ccmteamap/robot/3D_MODELS/3D_PCB.JPG

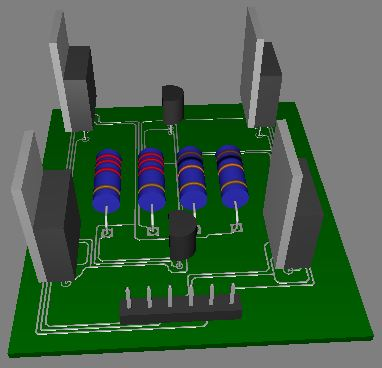
3D_MODELS/3D_PCB.JPG
