ccmteamap/robot/docs/analyse/mindmap.png

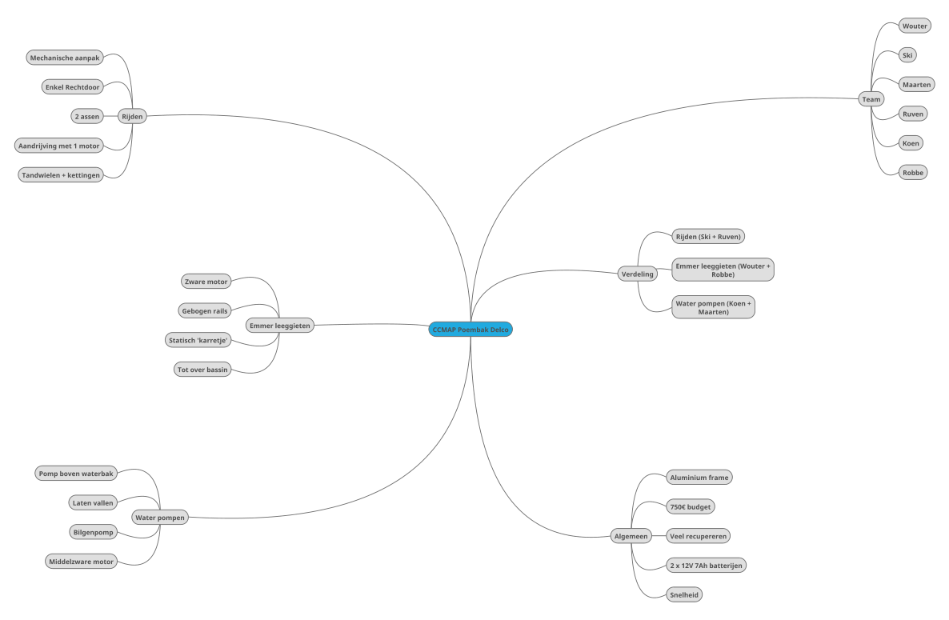
docs/analyse/mindmap.png
