ccmteamap/robot/docs/animations/pdelcogiforiginalfiles/001.jpg

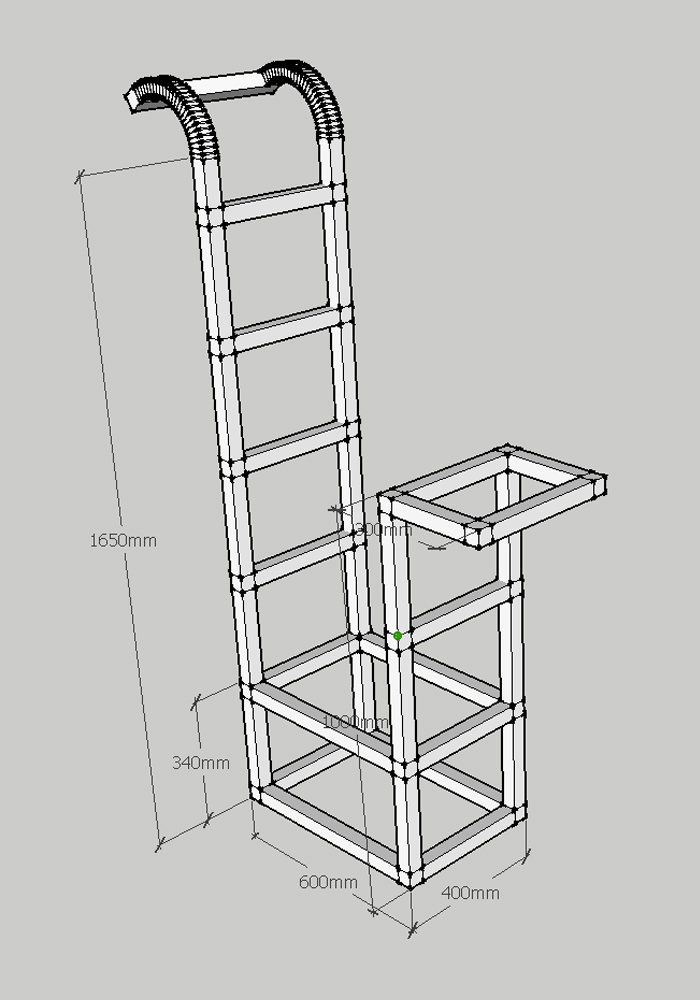
docs/animations/pdelcogiforiginalfiles/001.jpg
