ccmteamap/robot/docs/animations/pdelcogiforiginalfiles/003.jpg

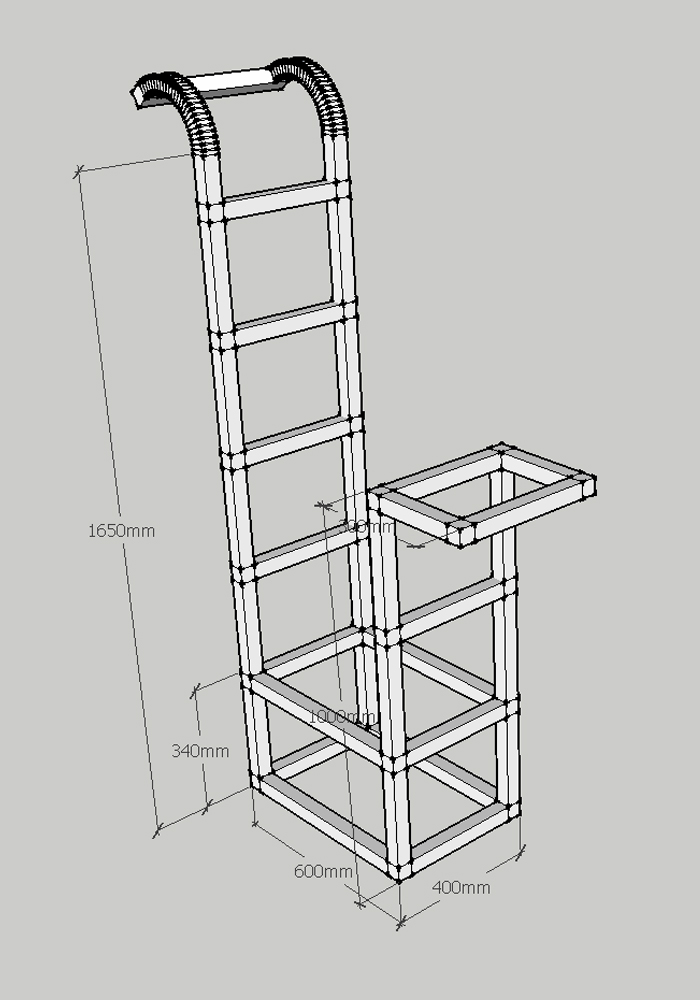
docs/animations/pdelcogiforiginalfiles/003.jpg
