ccmteamap/robot/docs/animations/pdelcogiforiginalfiles/005.jpg

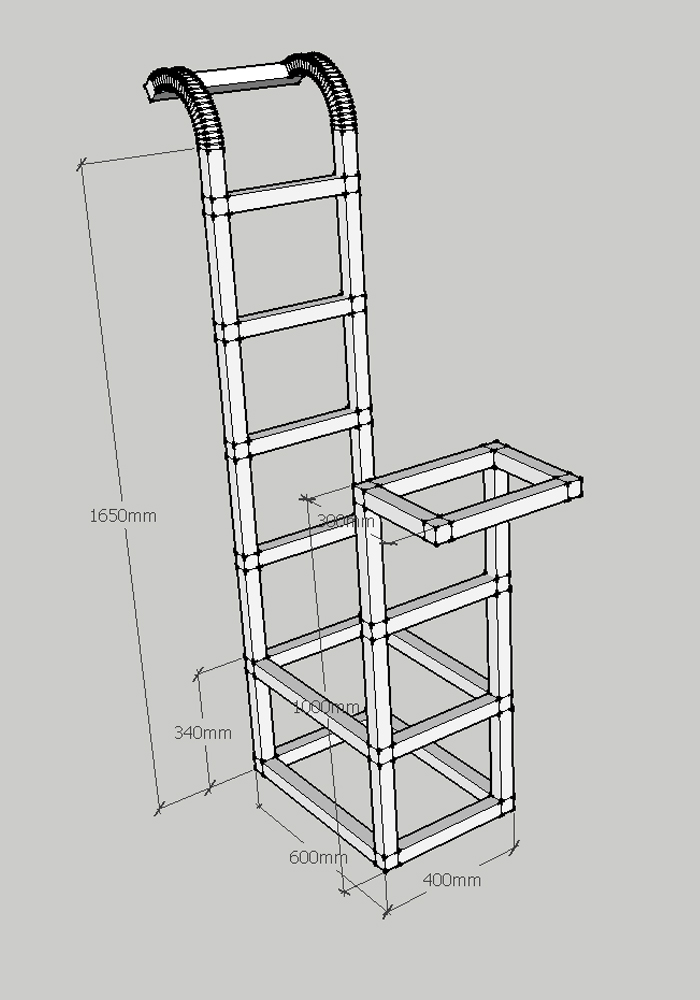
docs/animations/pdelcogiforiginalfiles/005.jpg
