ccmteamap/robot/docs/animations/pdelcogiforiginalfiles/006.jpg

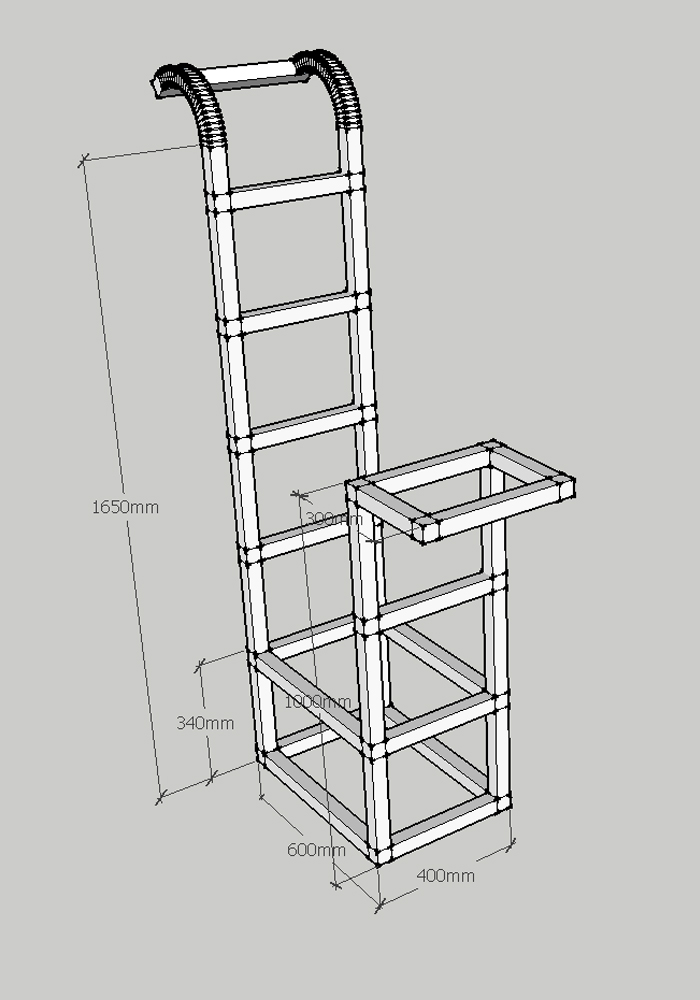
docs/animations/pdelcogiforiginalfiles/006.jpg
