ccmteamap/robot/docs/animations/pdelcogiforiginalfiles/008.jpg

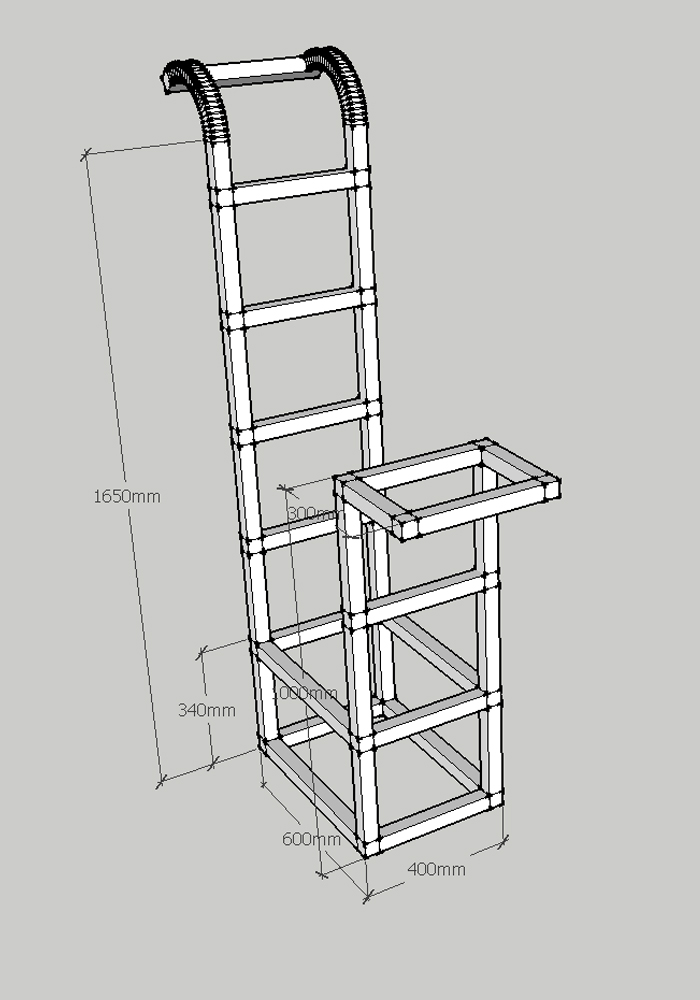
docs/animations/pdelcogiforiginalfiles/008.jpg
