ccmteamap/robot/docs/animations/pdelcogiforiginalfiles/012.jpg

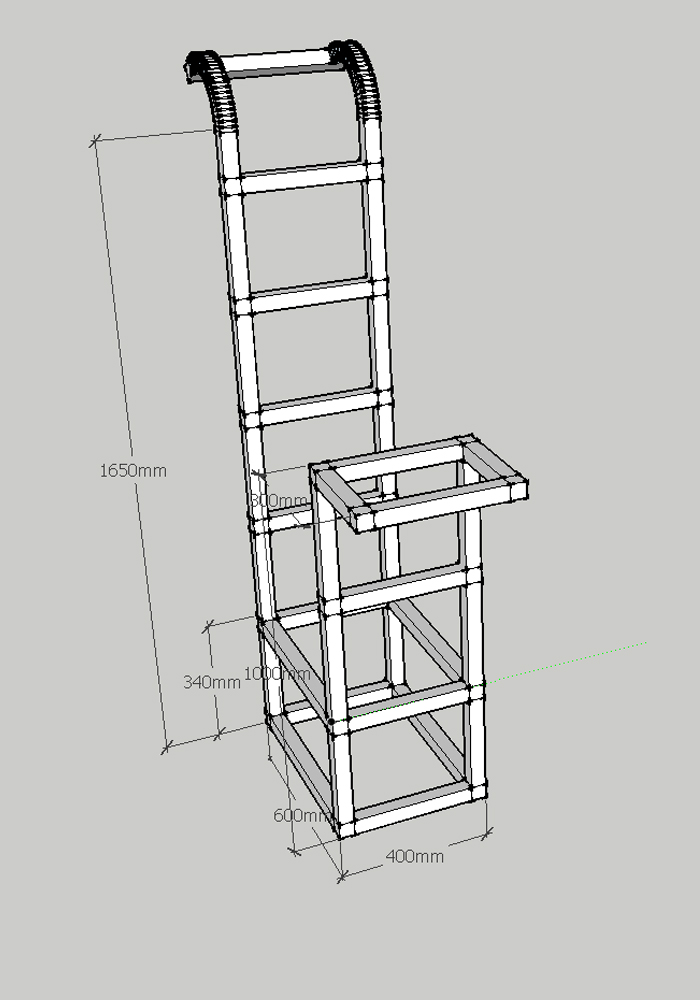
docs/animations/pdelcogiforiginalfiles/012.jpg
