ccmteamap/robot/docs/animations/pdelcogiforiginalfiles/014.jpg

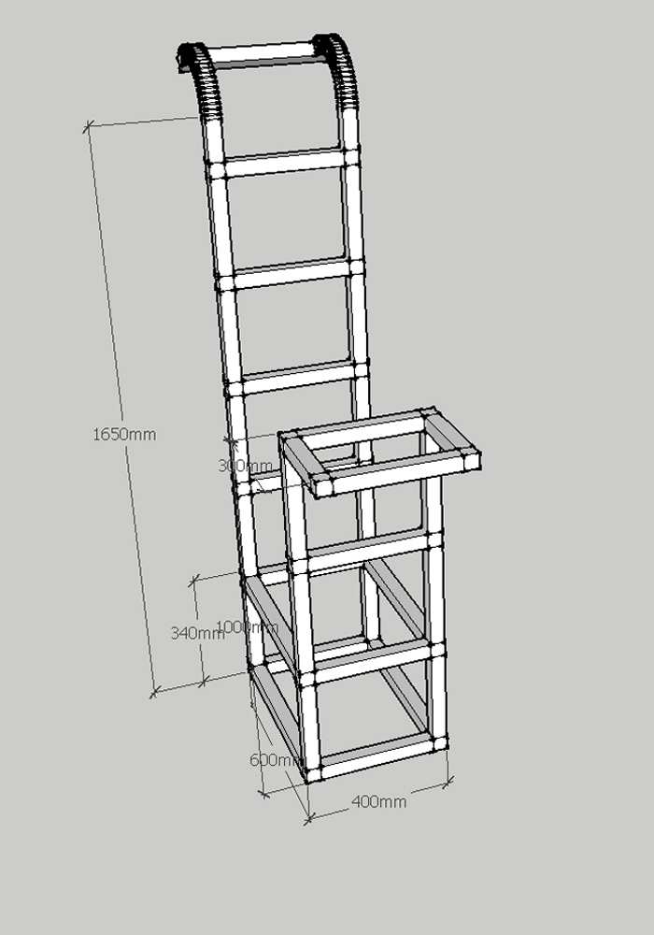
docs/animations/pdelcogiforiginalfiles/014.jpg
