ccmteamap/robot/docs/animations/pdelcogiforiginalfiles/015.jpg

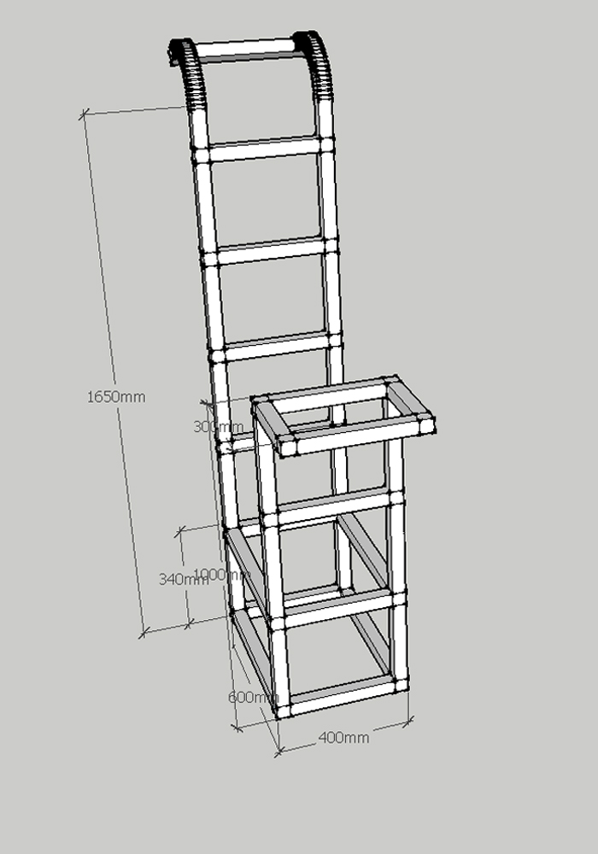
docs/animations/pdelcogiforiginalfiles/015.jpg
