ccmteamap/robot/docs/animations/pdelcogiforiginalfiles/016.jpg

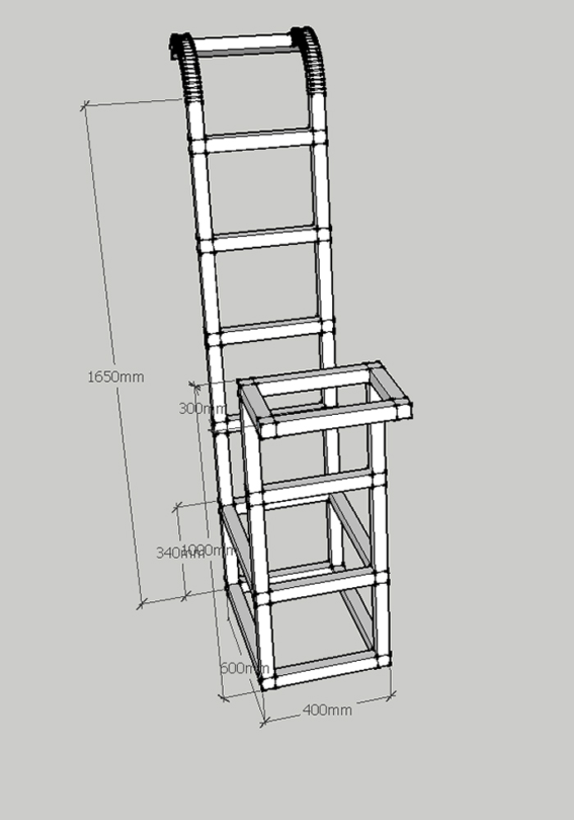
docs/animations/pdelcogiforiginalfiles/016.jpg
