ccmteamap/robot/docs/animations/pdelcogiforiginalfiles/017.jpg

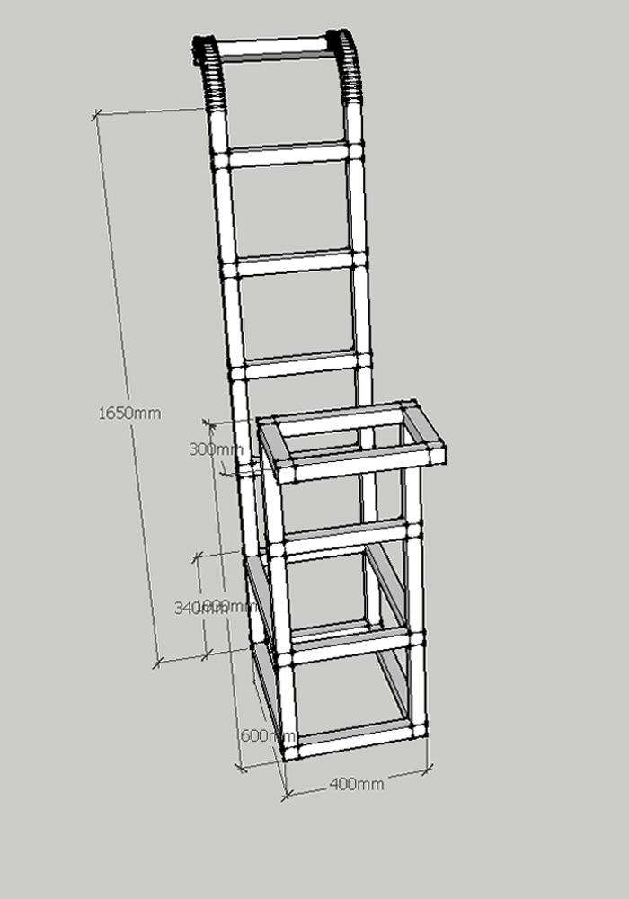
docs/animations/pdelcogiforiginalfiles/017.jpg
