ccmteamap/robot/docs/animations/pdelcogiforiginalfiles/018.jpg

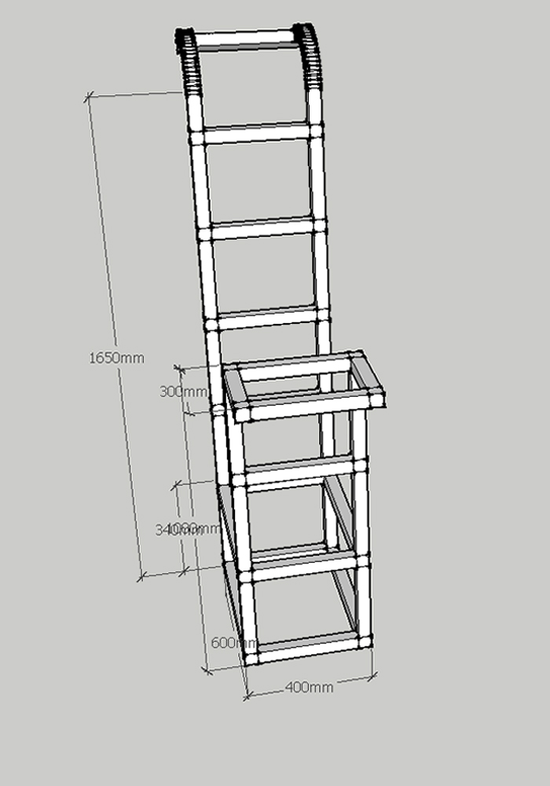
docs/animations/pdelcogiforiginalfiles/018.jpg
