ccmteamap/robot/docs/animations/pdelcogiforiginalfiles/020.jpg

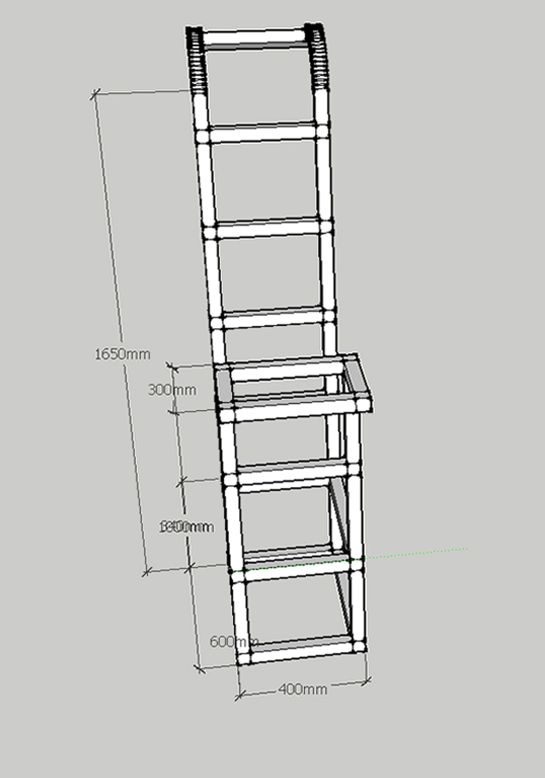
docs/animations/pdelcogiforiginalfiles/020.jpg
