ccmteamap/robot/docs/animations/pdelcogiforiginalfiles/021.jpg

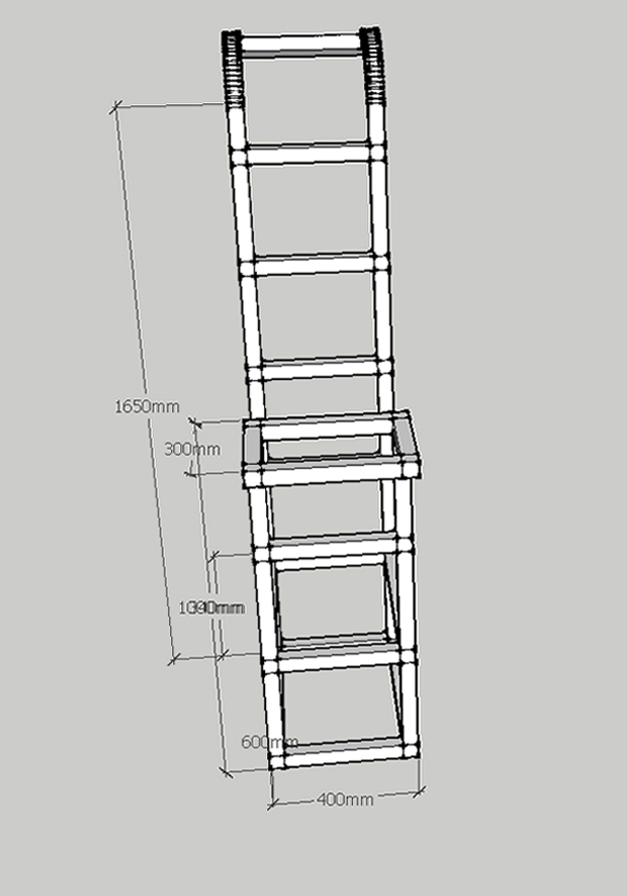
docs/animations/pdelcogiforiginalfiles/021.jpg
