ccmteamap/robot/docs/animations/pdelcogiforiginalfiles/022.jpg

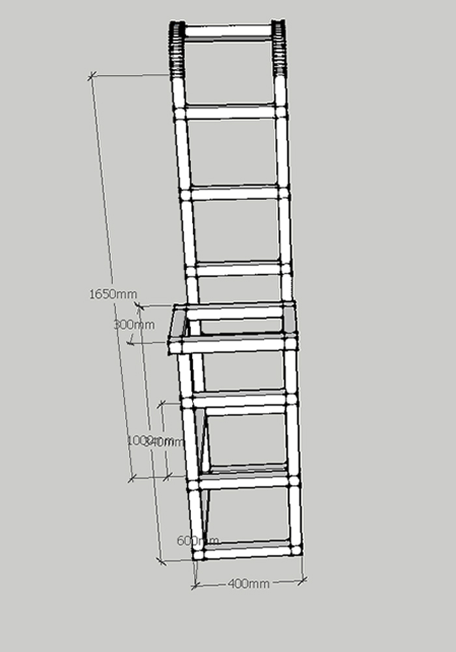
docs/animations/pdelcogiforiginalfiles/022.jpg
