ccmteamap/robot/docs/animations/pdelcogiforiginalfiles/024.jpg

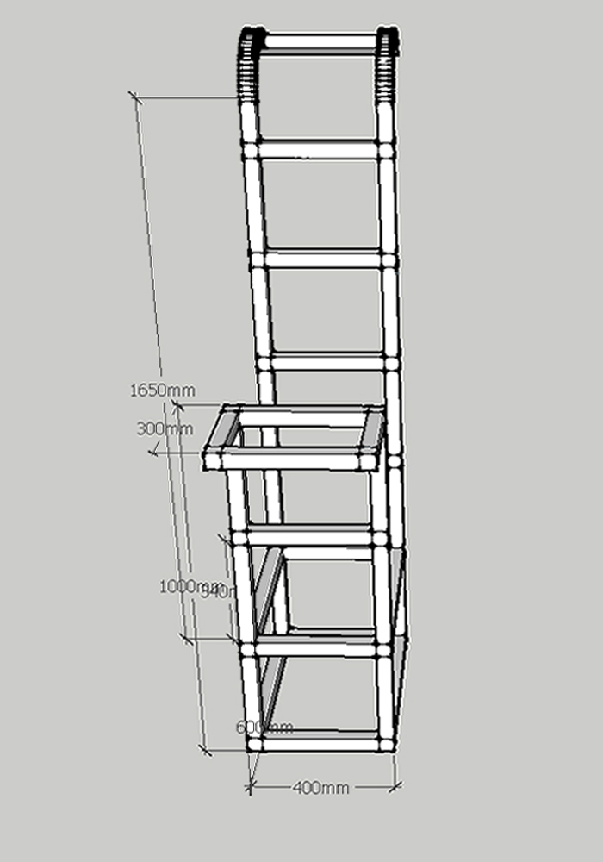
docs/animations/pdelcogiforiginalfiles/024.jpg
