ccmteamap/robot/docs/animations/pdelcogiforiginalfiles/025.jpg

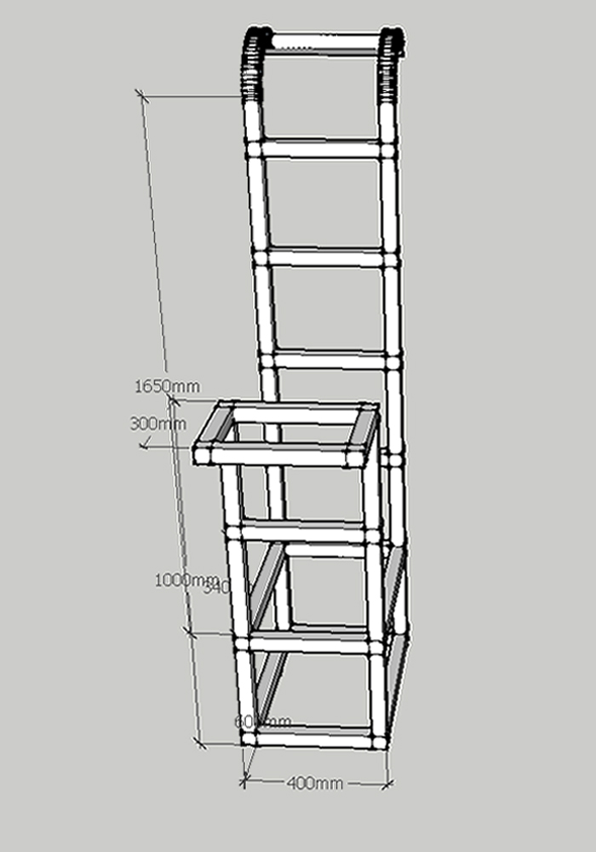
docs/animations/pdelcogiforiginalfiles/025.jpg
