ccmteamap/robot/docs/animations/pdelcogiforiginalfiles/026.jpg

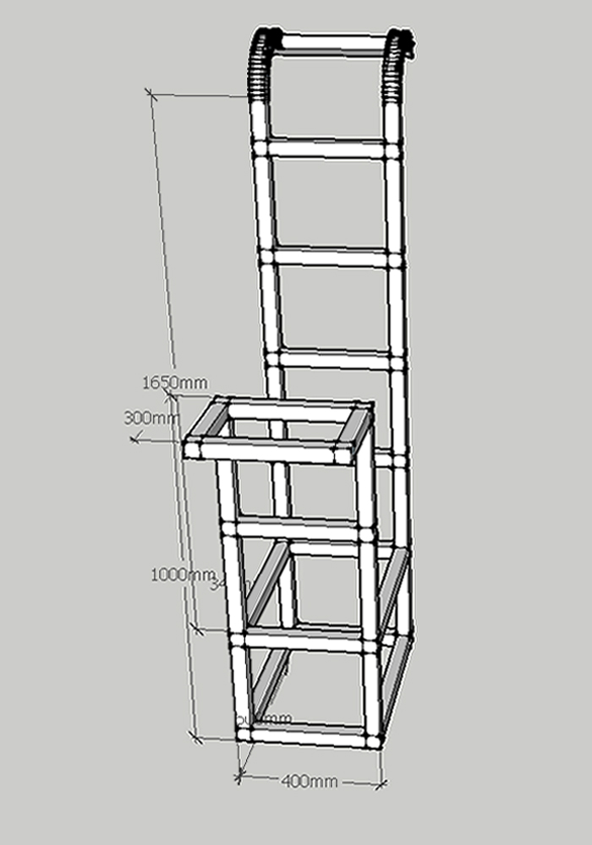
docs/animations/pdelcogiforiginalfiles/026.jpg
