ccmteamap/robot/docs/animations/pdelcogiforiginalfiles/027.jpg

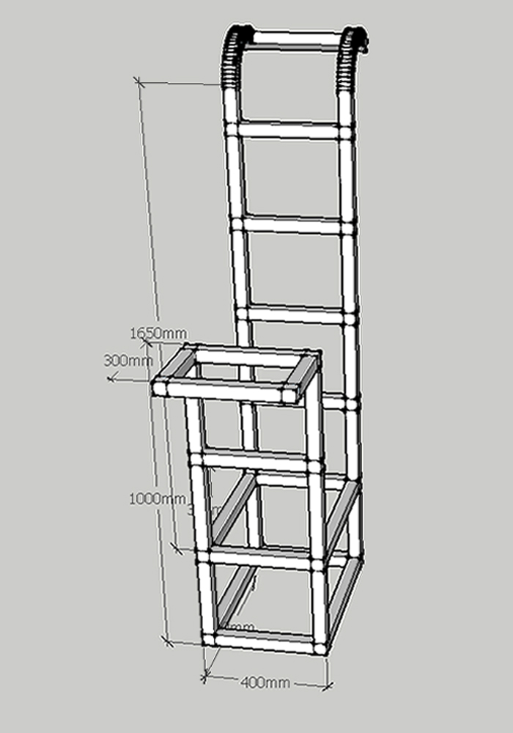
docs/animations/pdelcogiforiginalfiles/027.jpg
