ccmteamap/robot/docs/animations/pdelcogiforiginalfiles/028.jpg

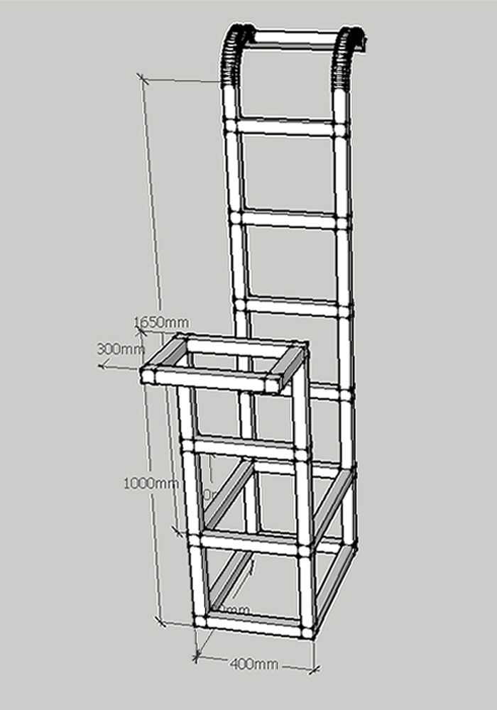
docs/animations/pdelcogiforiginalfiles/028.jpg
