ccmteamap/robot/docs/animations/pdelcogiforiginalfiles/031.jpg

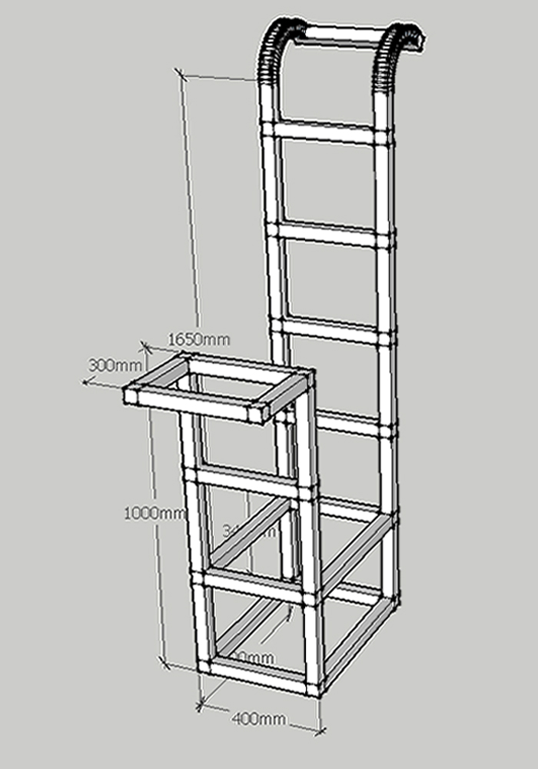
docs/animations/pdelcogiforiginalfiles/031.jpg
