ccmteamap/robot/docs/animations/pdelcogiforiginalfiles/032.jpg

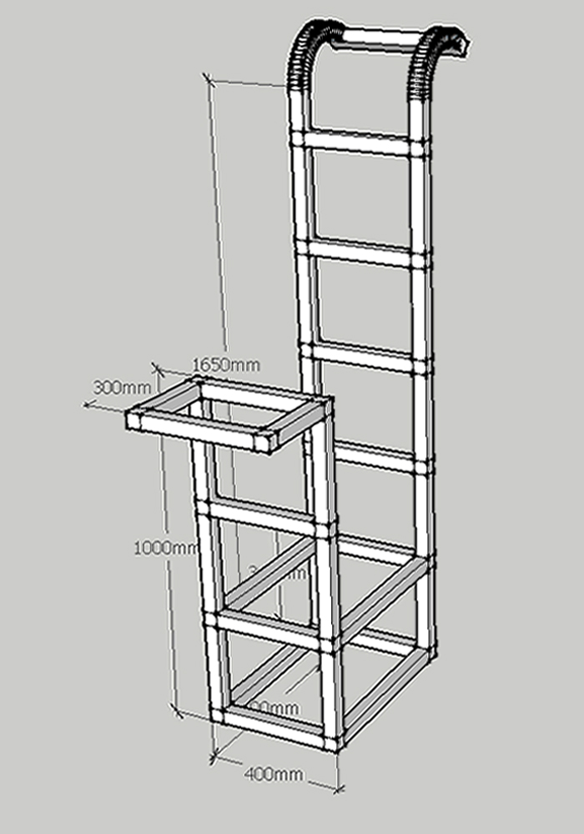
docs/animations/pdelcogiforiginalfiles/032.jpg
