ccmteamap/robot/docs/animations/pdelcogiforiginalfiles/033.jpg

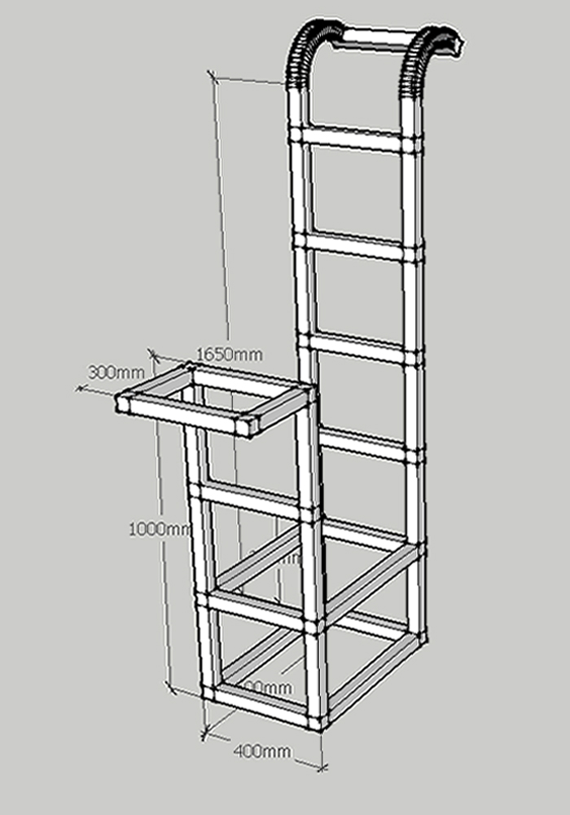
docs/animations/pdelcogiforiginalfiles/033.jpg
