ccmteamap/robot/docs/animations/pdelcogiforiginalfiles/034.jpg

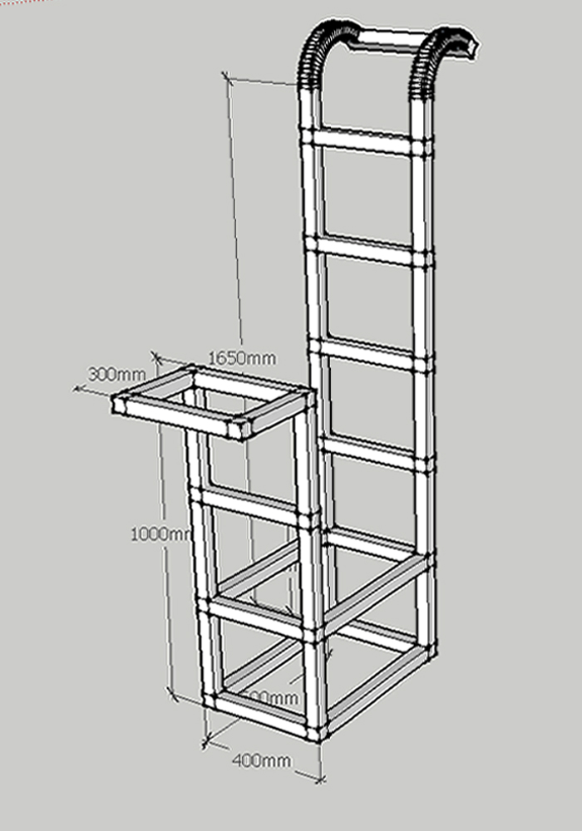
docs/animations/pdelcogiforiginalfiles/034.jpg
