ccmteamap/robot/docs/animations/pdelcogiforiginalfiles/035.jpg

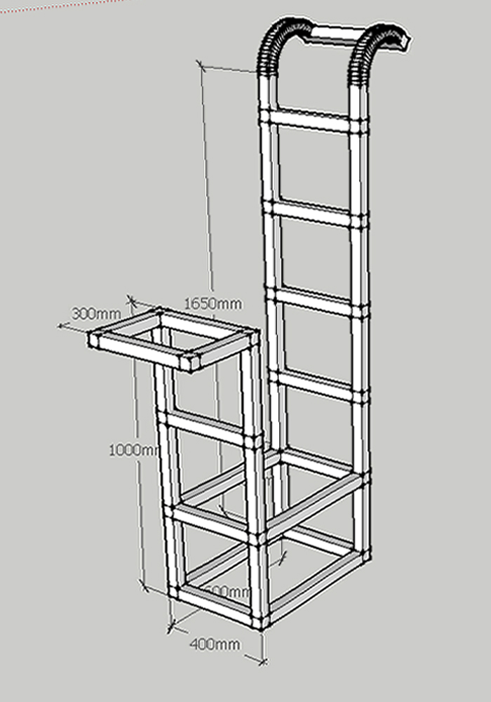
docs/animations/pdelcogiforiginalfiles/035.jpg
