ccmteamap/robot/docs/animations/pdelcogiforiginalfiles/036.jpg

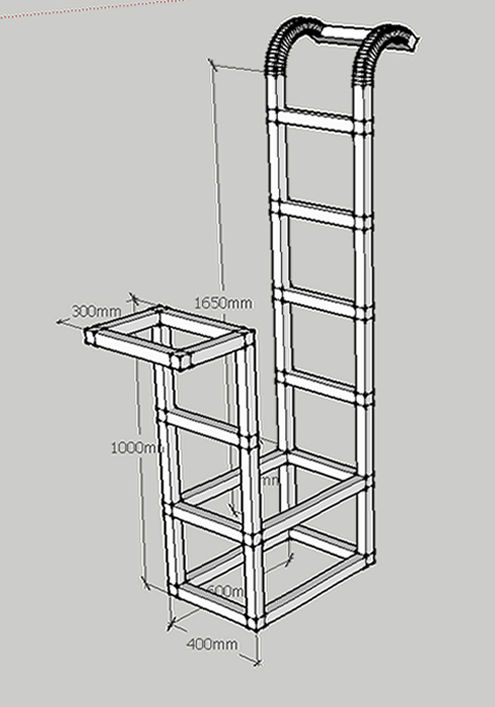
docs/animations/pdelcogiforiginalfiles/036.jpg
