ccmteamap/robot/docs/animations/pdelcogiforiginalfiles/037.jpg

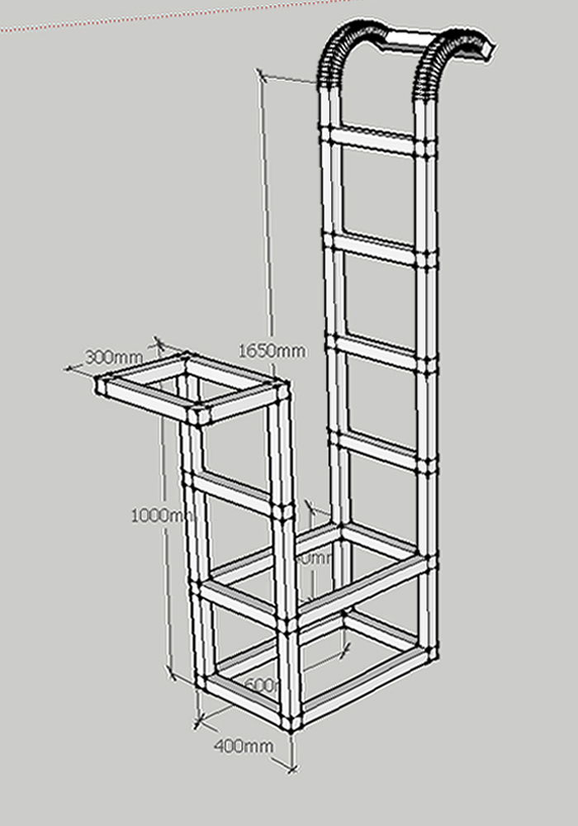
docs/animations/pdelcogiforiginalfiles/037.jpg
