ccmteamap/robot/docs/animations/pdelcogiforiginalfiles/040.jpg

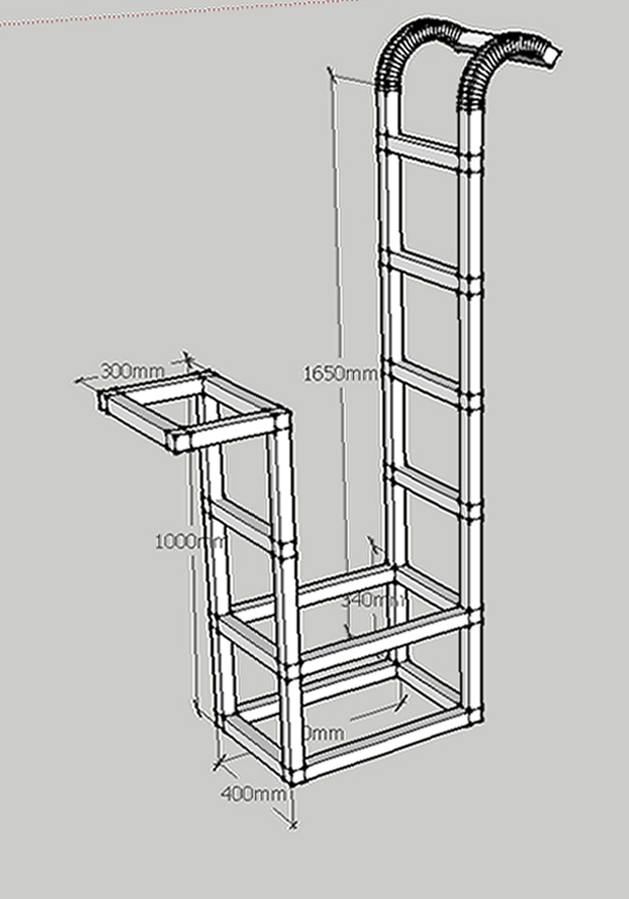
docs/animations/pdelcogiforiginalfiles/040.jpg
