ccmteamap/robot/docs/animations/pdelcogiforiginalfiles/045.jpg

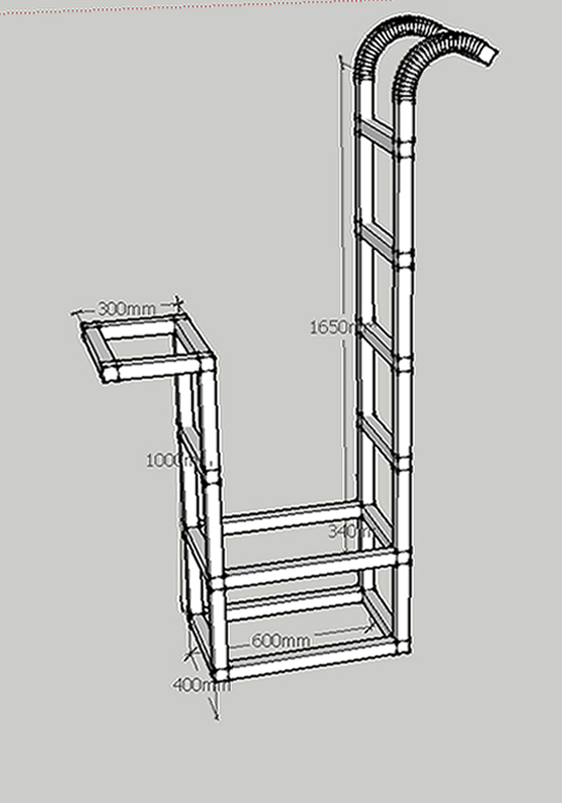
docs/animations/pdelcogiforiginalfiles/045.jpg
