ccmteamap/robot/docs/animations/pdelcogiforiginalfiles/047.jpg

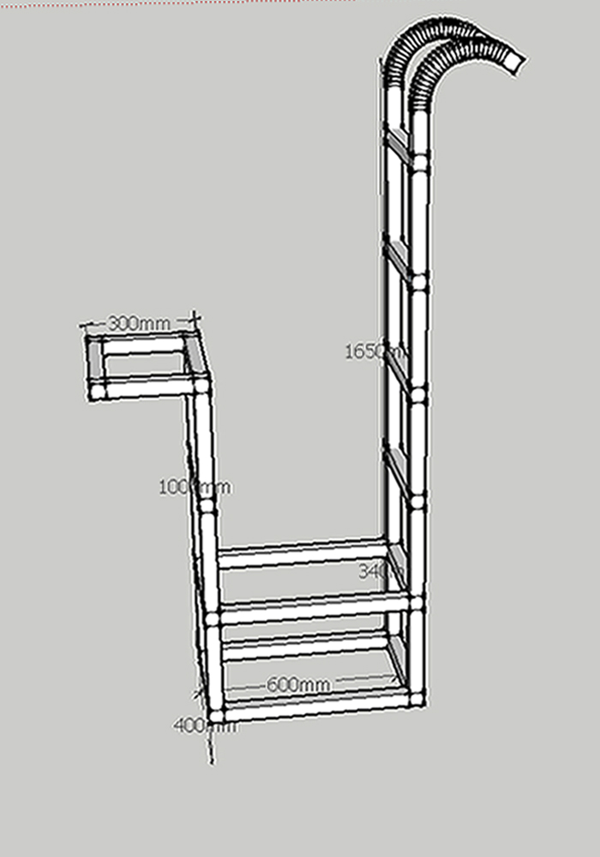
docs/animations/pdelcogiforiginalfiles/047.jpg
