ccmteamap/robot/docs/animations/pdelcogiforiginalfiles/048.jpg

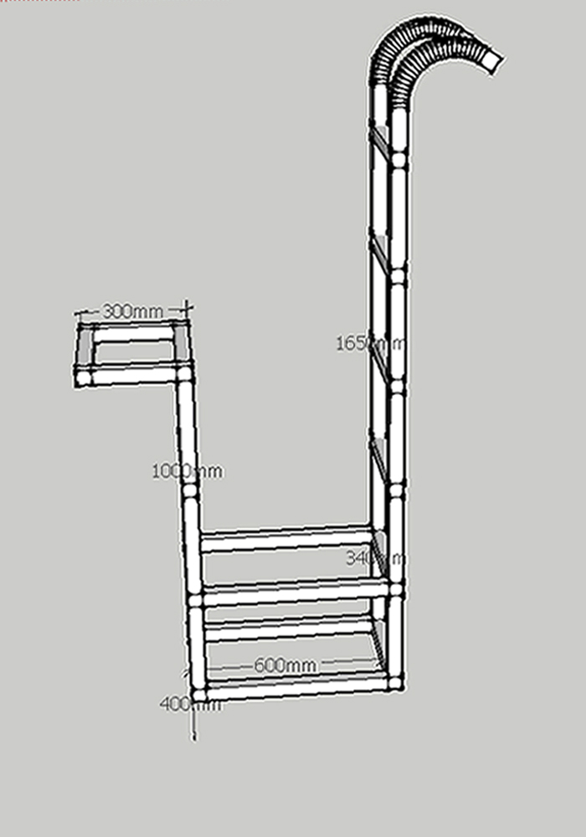
docs/animations/pdelcogiforiginalfiles/048.jpg
