ccmteamap/robot/docs/animations/pdelcogiforiginalfiles/051.jpg

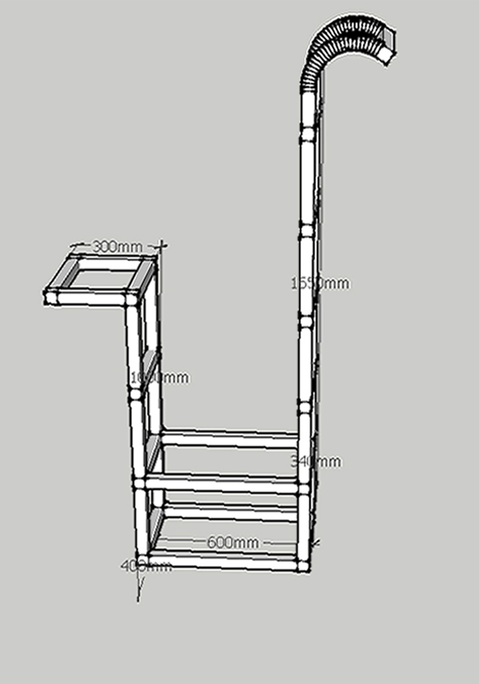
docs/animations/pdelcogiforiginalfiles/051.jpg
