ccmteamap/robot/docs/animations/pdelcogiforiginalfiles/054.jpg

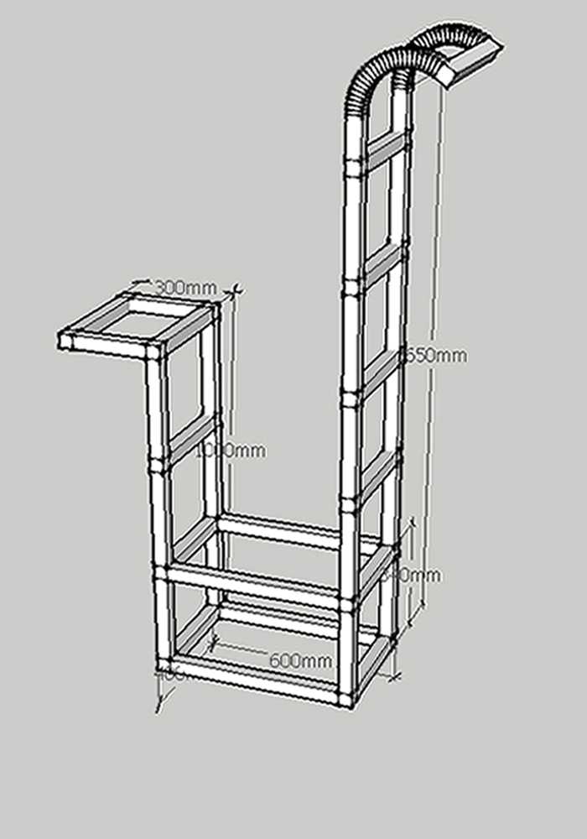
docs/animations/pdelcogiforiginalfiles/054.jpg
