ccmteamap/robot/docs/animations/pdelcogiforiginalfiles/055.jpg

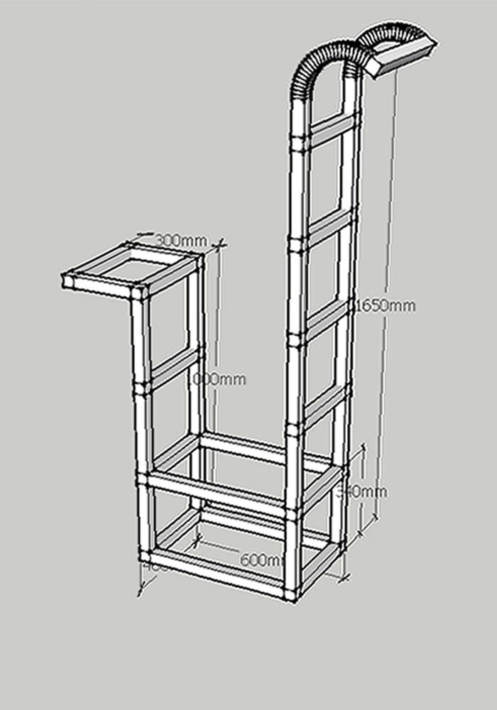
docs/animations/pdelcogiforiginalfiles/055.jpg
