ccmteamap/robot/docs/animations/pdelcogiforiginalfiles/056.jpg

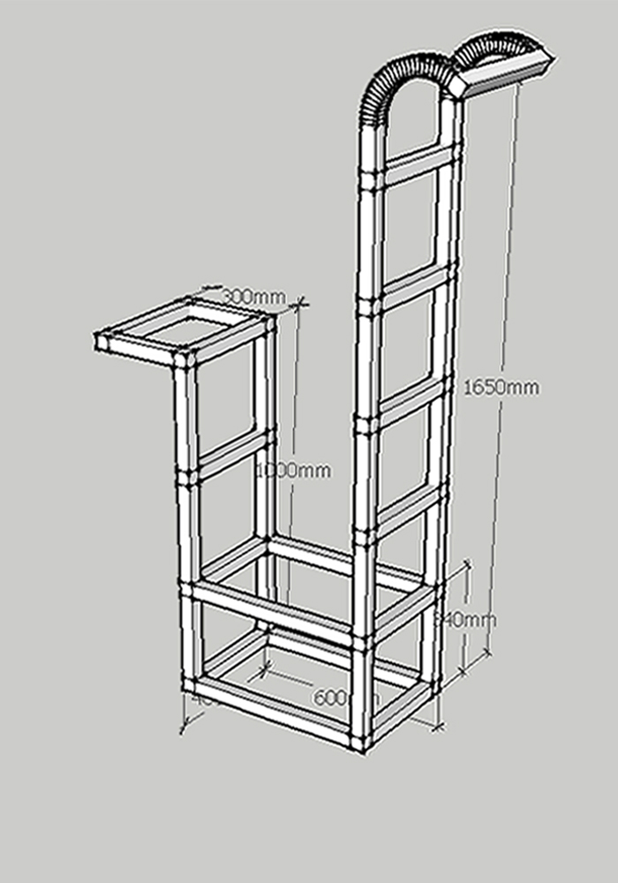
docs/animations/pdelcogiforiginalfiles/056.jpg
