ccmteamap/robot/docs/animations/pdelcogiforiginalfiles/057.jpg

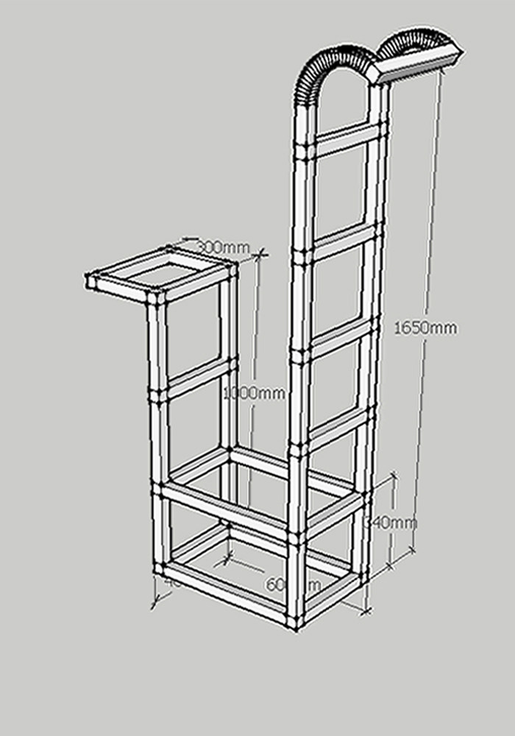
docs/animations/pdelcogiforiginalfiles/057.jpg
