ccmteamap/robot/docs/animations/pdelcogiforiginalfiles/058.jpg

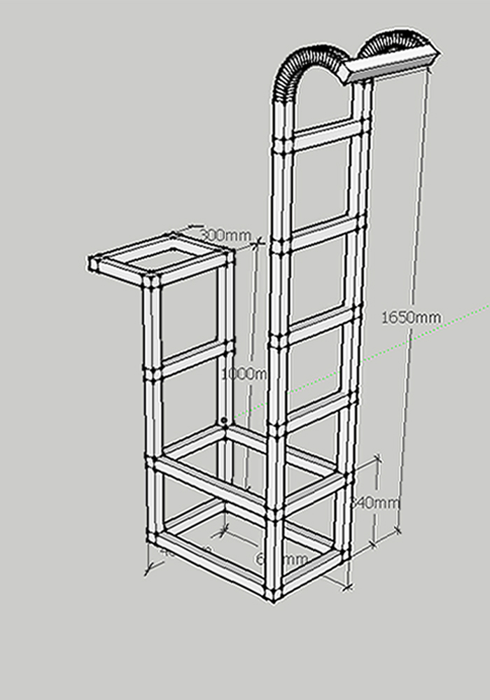
docs/animations/pdelcogiforiginalfiles/058.jpg
