ccmteamap/robot/docs/animations/pdelcogiforiginalfiles/060.jpg

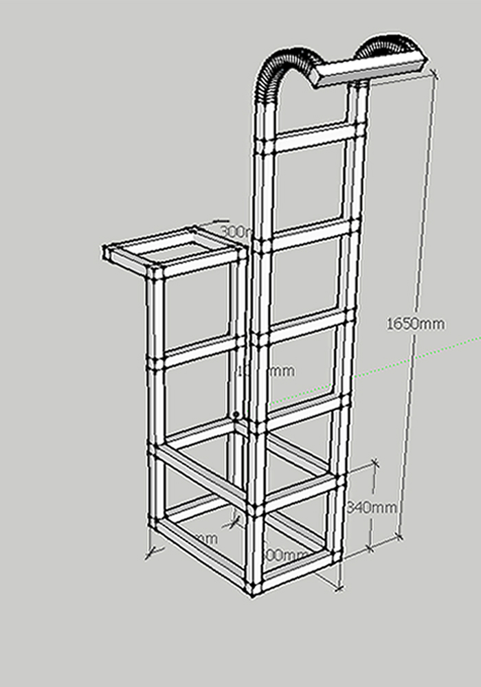
docs/animations/pdelcogiforiginalfiles/060.jpg
