ccmteamap/robot/docs/animations/pdelcogiforiginalfiles/061.jpg

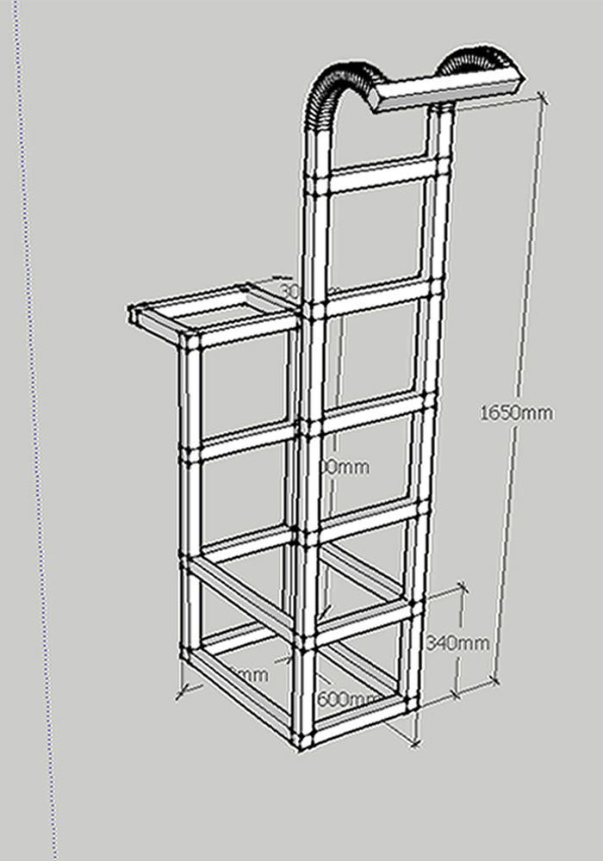
docs/animations/pdelcogiforiginalfiles/061.jpg
