ccmteamap/robot/docs/animations/Robot.png

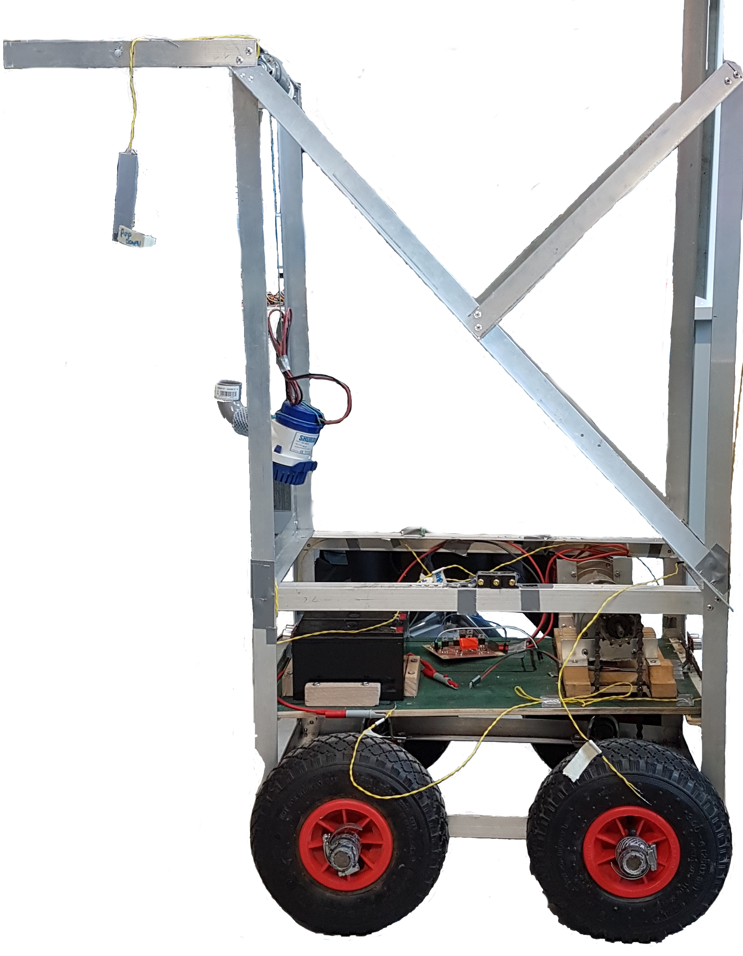
docs/animations/Robot.png
