ccmteamap/robot/docs/photos/20170310_133426.jpg

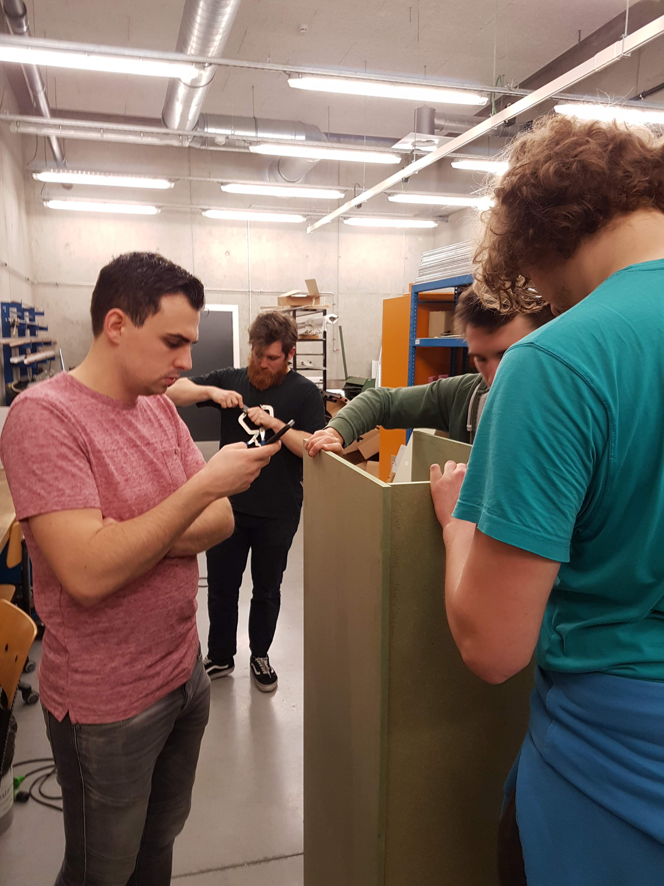
docs/photos/20170310_133426.jpg
