ccmteamap/robot/docs/photos/20170310_133432.jpg

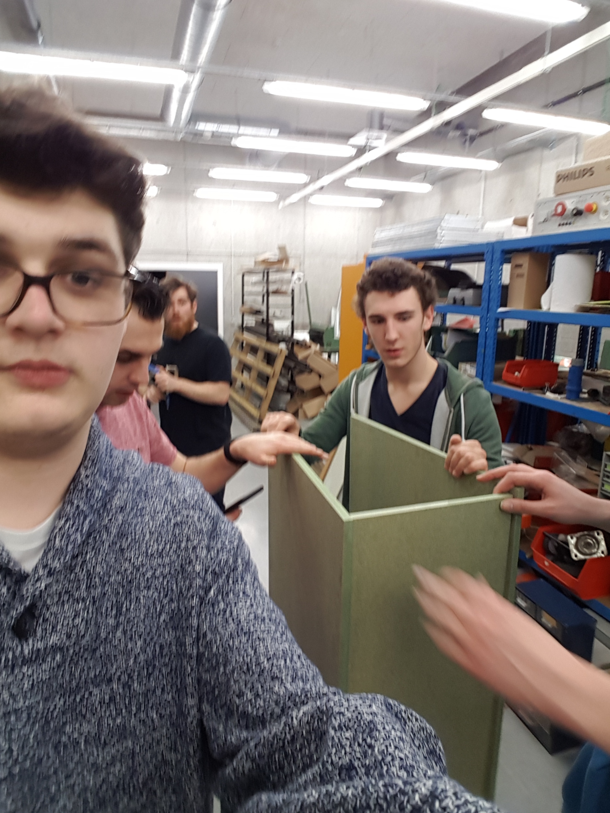
docs/photos/20170310_133432.jpg
