ccmteamap/robot/docs/photos/20170310_133632.jpg

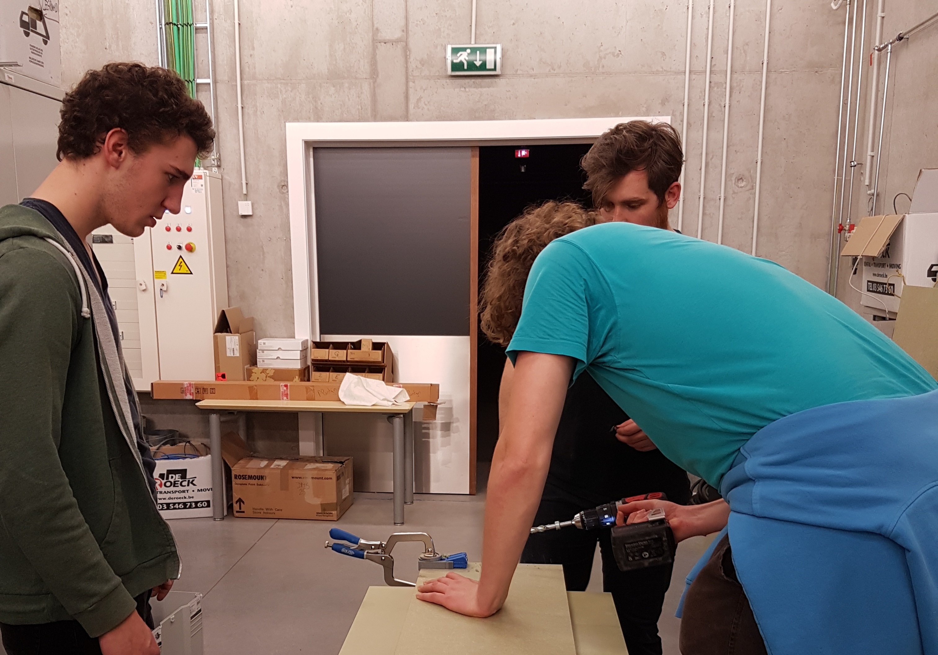
docs/photos/20170310_133632.jpg
