ccmteamap/robot/docs/photos/20170310_134215.jpg

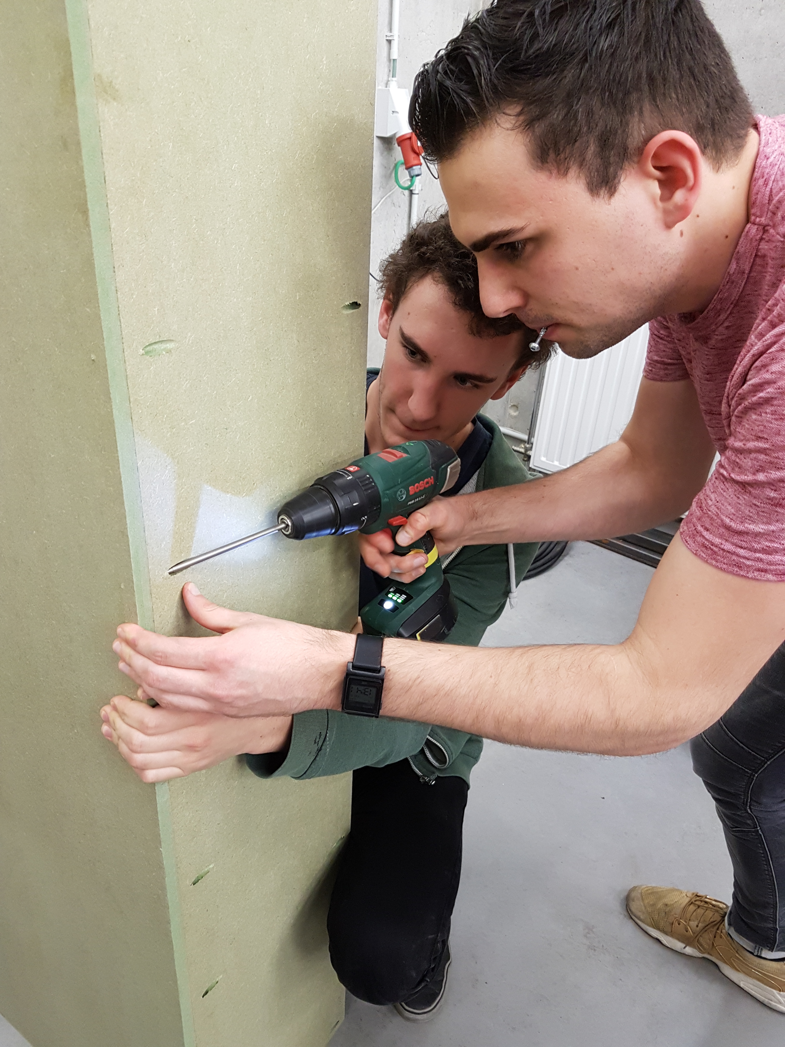
docs/photos/20170310_134215.jpg
