ccmteamap/robot/docs/photos/20170327_142244.jpg

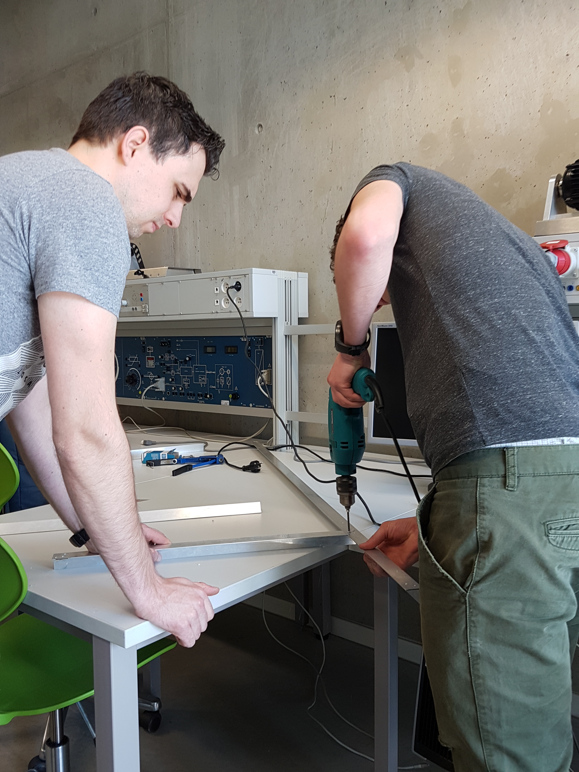
docs/photos/20170327_142244.jpg
