ccmteamap/robot/docs/photos/20170327_143322.jpg

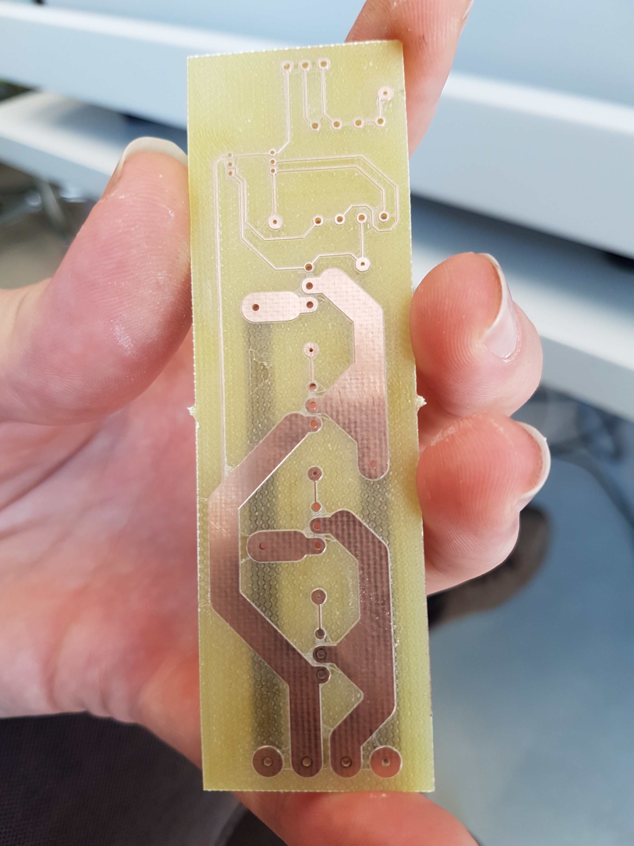
docs/photos/20170327_143322.jpg
