ccmteamap/robot/docs/photos/20170327_143832.jpg

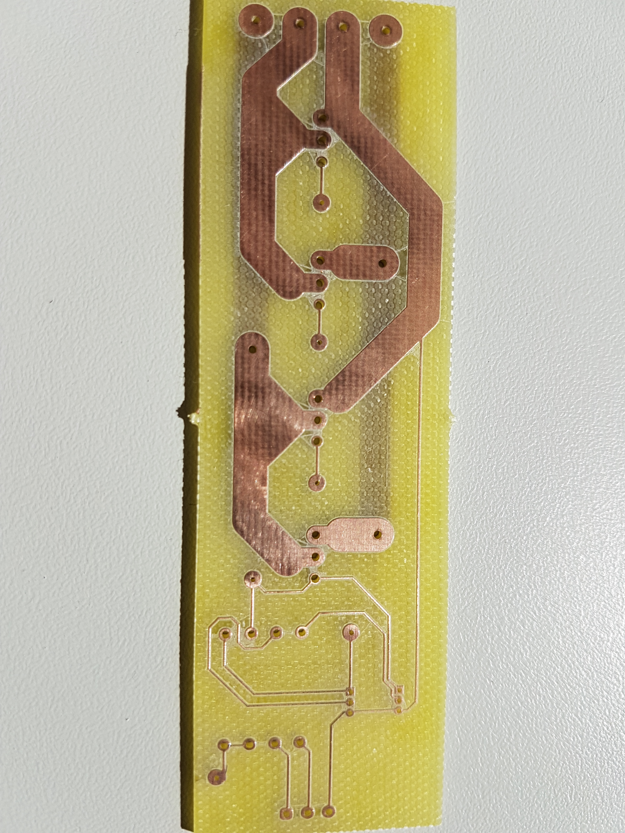
docs/photos/20170327_143832.jpg
