ccmteamap/robot/docs/photos/IMG_20170310_133601.jpg

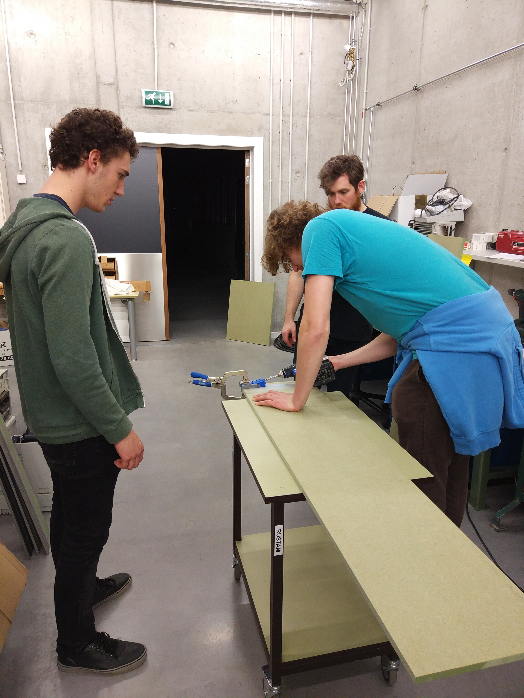
docs/photos/IMG_20170310_133601.jpg
