ccmteamap/robot/docs/photos/IMG_20170310_133729.jpg

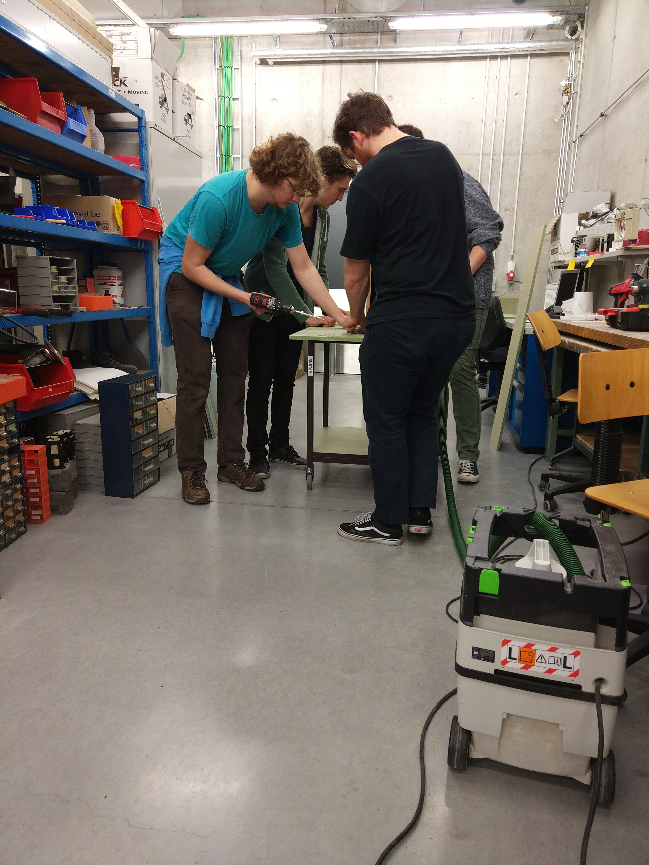
docs/photos/IMG_20170310_133729.jpg
