ccmteamap/robot/docs/photos/IMG_20170310_133730.jpg

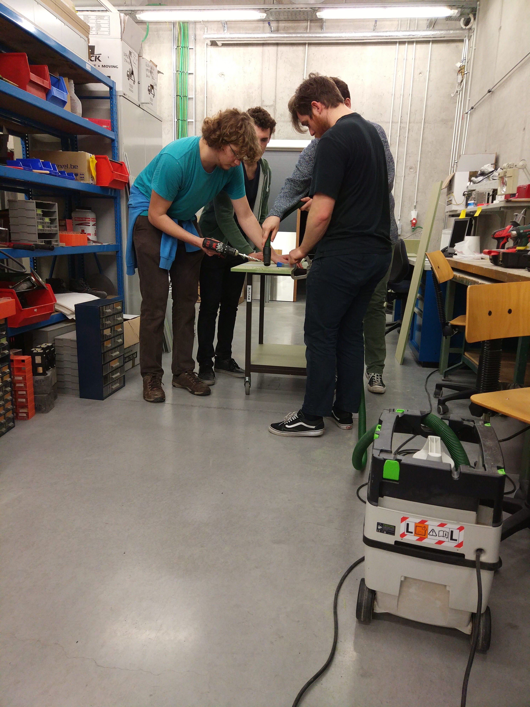
docs/photos/IMG_20170310_133730.jpg
