ccmteamap/robot/docs/photos/IMG_20170310_133733.jpg

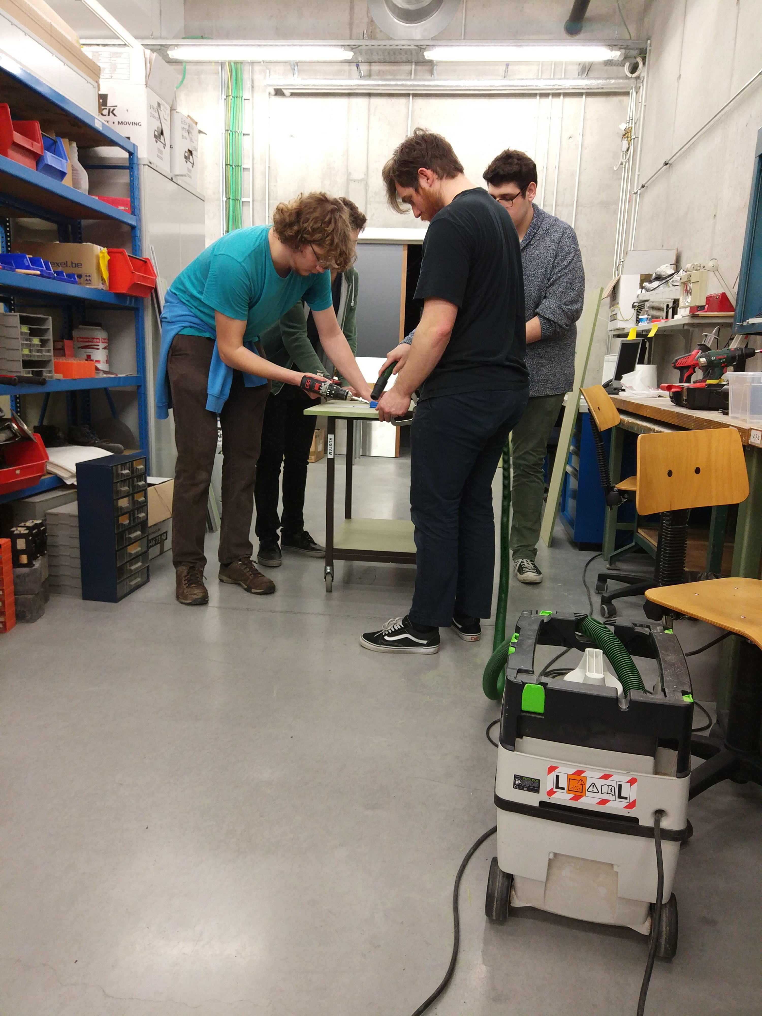
docs/photos/IMG_20170310_133733.jpg
