ccmteamap/robot/docs/photos/IMG_20170310_135600.jpg

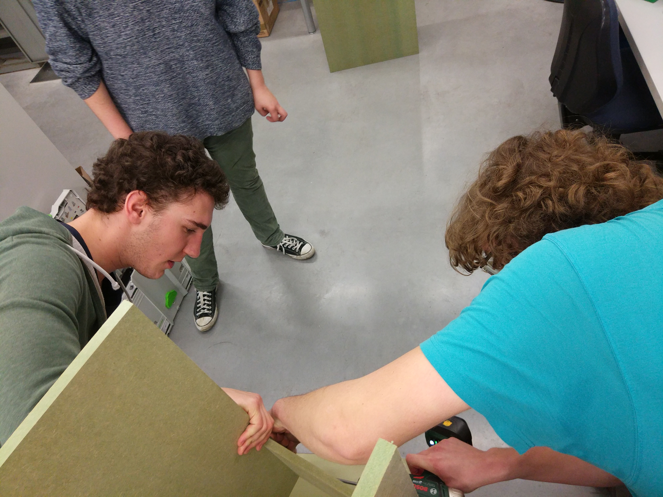
docs/photos/IMG_20170310_135600.jpg
