ccmteamap/robot/docs/photos/IMG_20170310_135602.jpg

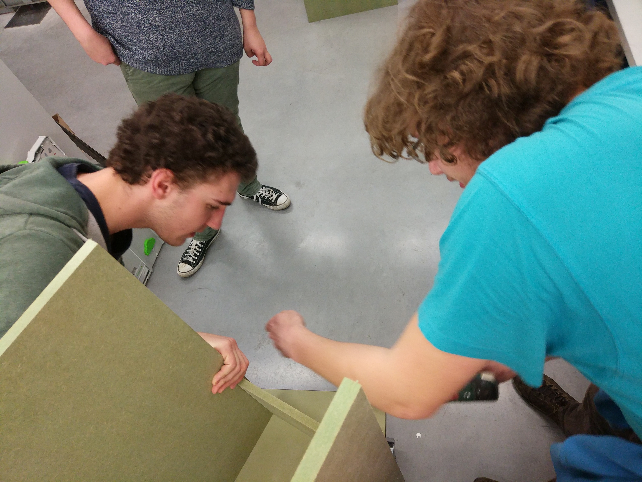
docs/photos/IMG_20170310_135602.jpg
