ccmteamap/robot/docs/photos/IMG_20170310_135609.jpg

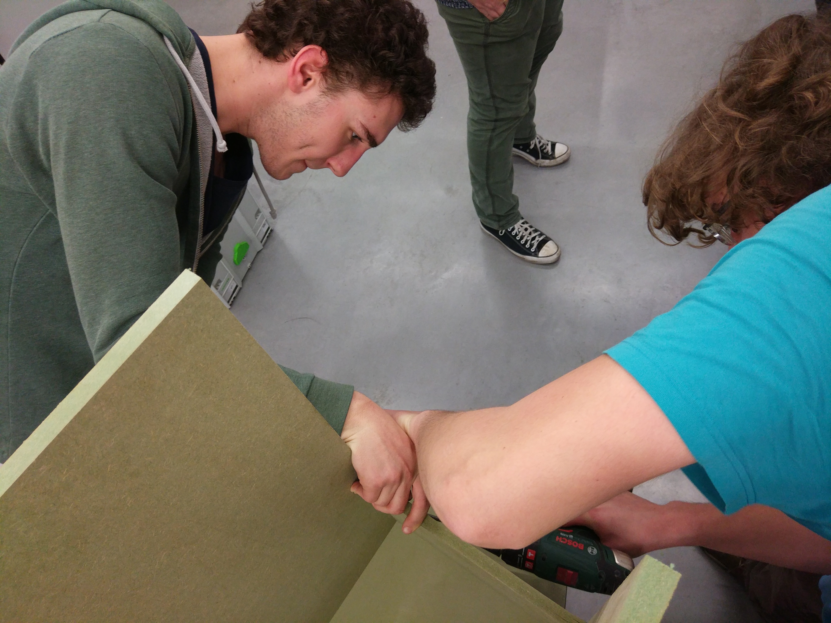
docs/photos/IMG_20170310_135609.jpg
