ccmteamap/robot/docs/photos/IMG_20170310_135611.jpg

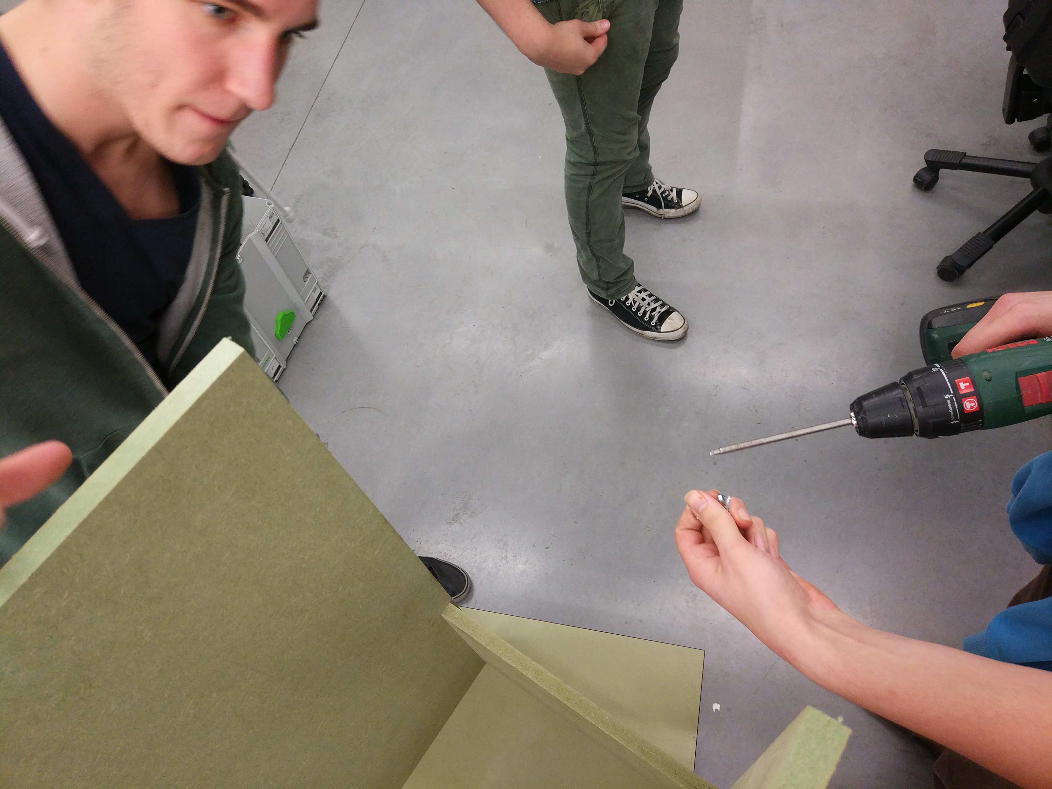
docs/photos/IMG_20170310_135611.jpg
