ccmteamap/robot/docs/photos/IMG_20170310_135938.jpg

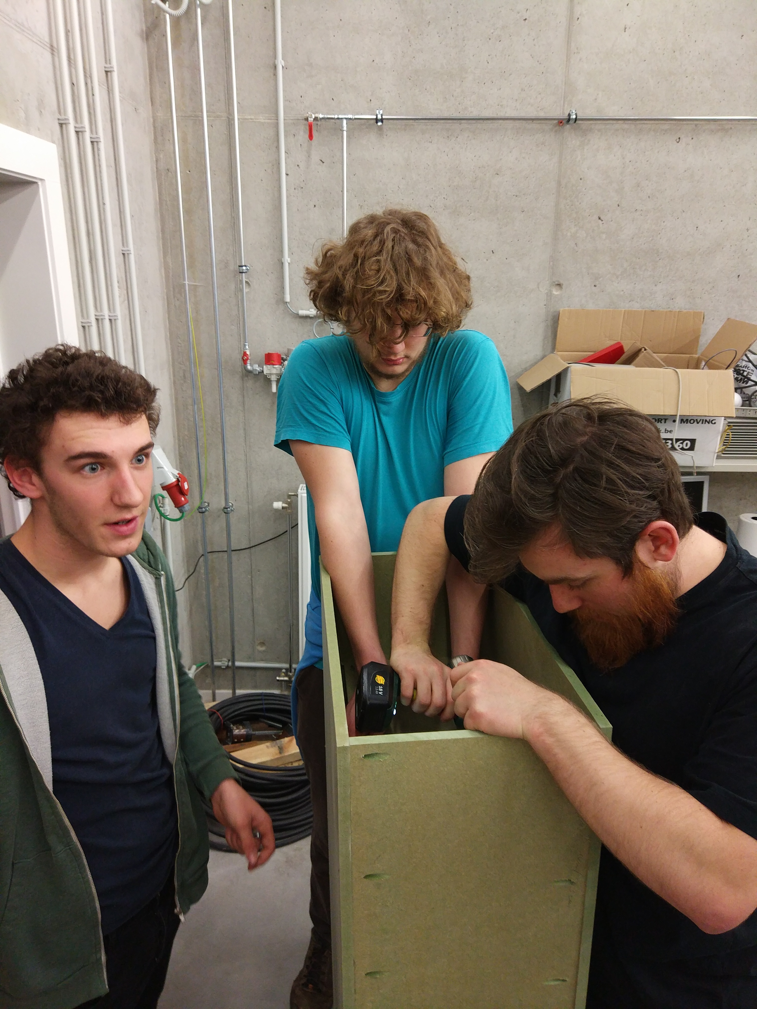
docs/photos/IMG_20170310_135938.jpg
