ccmteamap/robot/docs/photos/IMG_20170320_085642.jpg

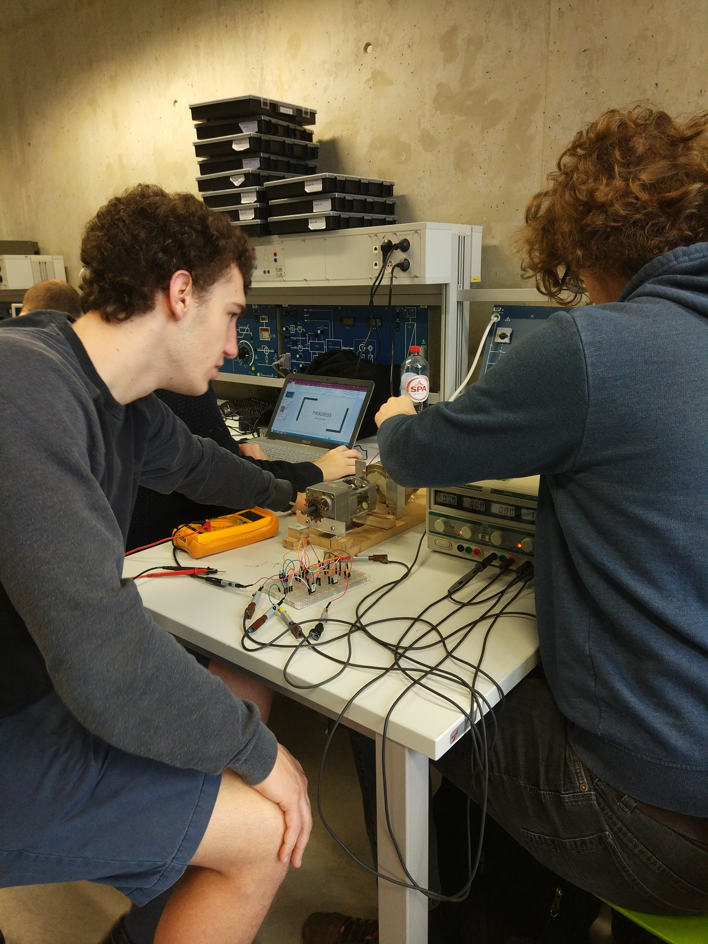
docs/photos/IMG_20170320_085642.jpg
