ccmteamap/robot/docs/photos/IMG_20170320_085652.jpg

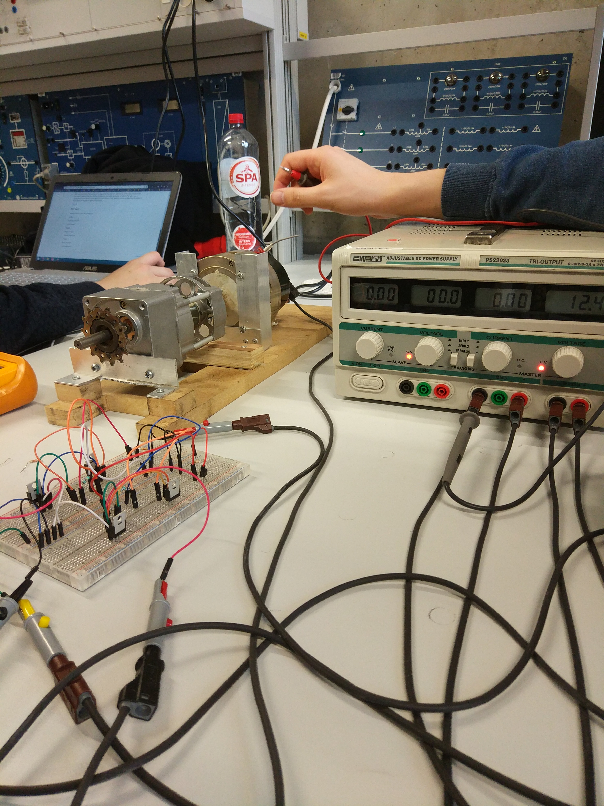
docs/photos/IMG_20170320_085652.jpg
