ccmteamap/robot/docs/photos/IMG_20170320_093129.jpg

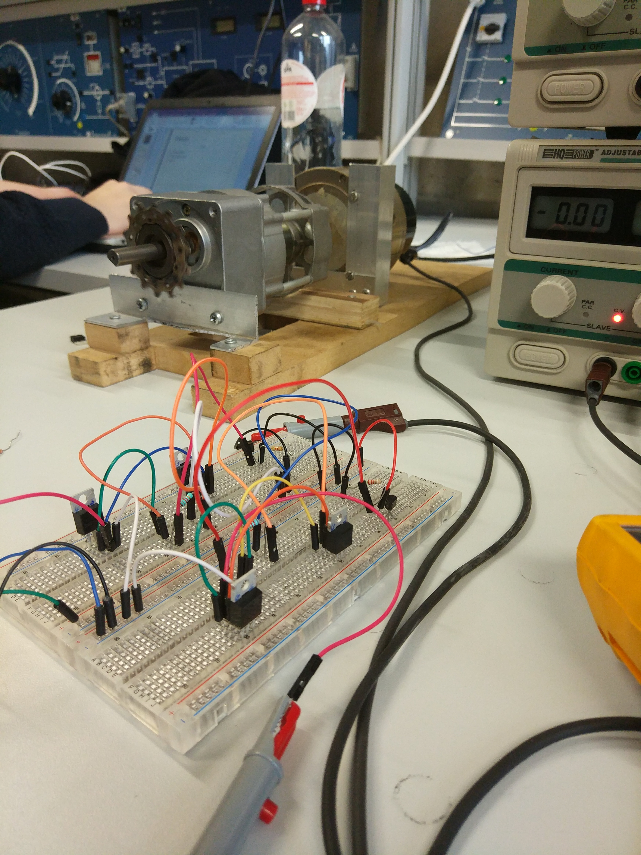
docs/photos/IMG_20170320_093129.jpg
