ccmteamap/robot/docs/photos/IMG_20170320_095238.jpg

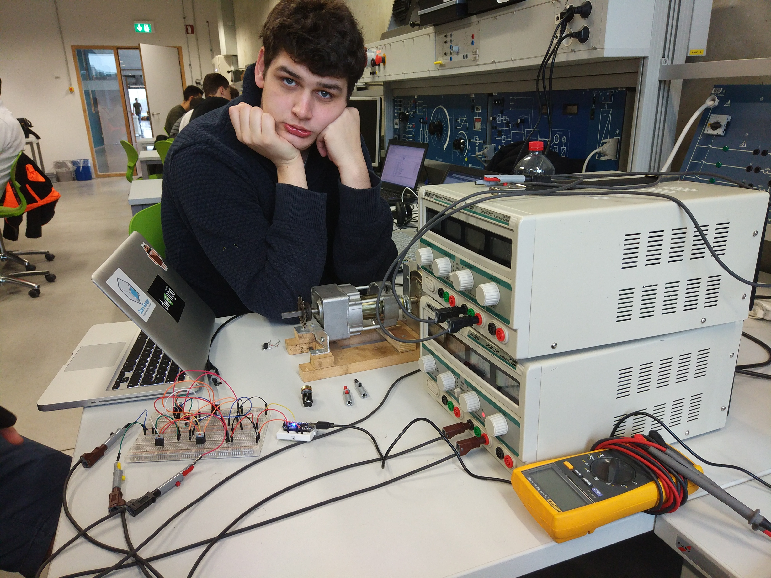
docs/photos/IMG_20170320_095238.jpg
