ccmteamap/robot/docs/photos/IMG_20170327_133035.jpg

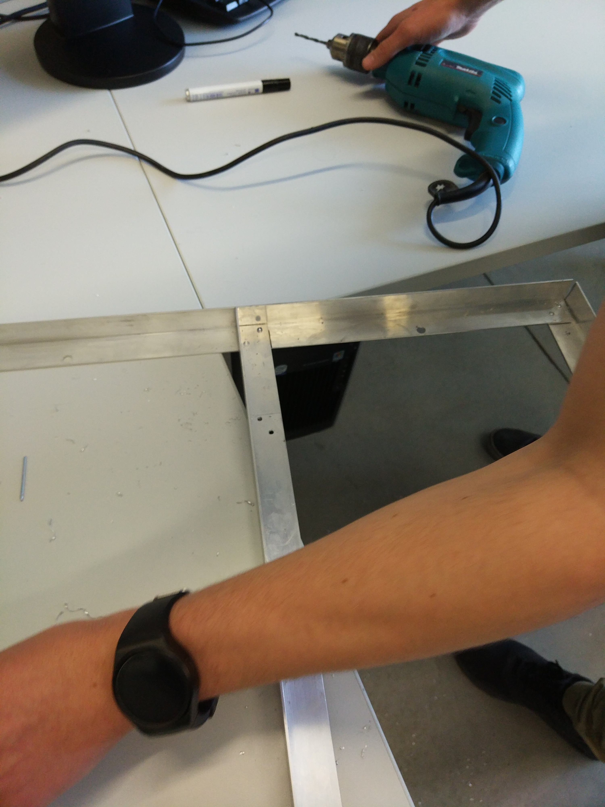
docs/photos/IMG_20170327_133035.jpg
