ccmteamap/robot/docs/photos/IMG_20170327_133036.jpg

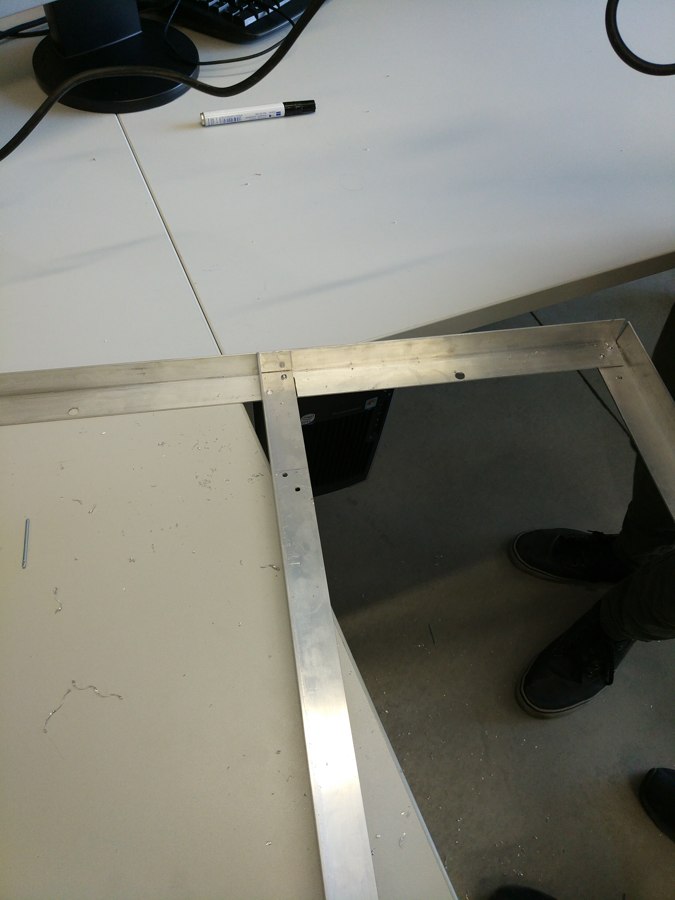
docs/photos/IMG_20170327_133036.jpg
