ccmteamap/robot/docs/photos/IMG_20170327_133126.jpg

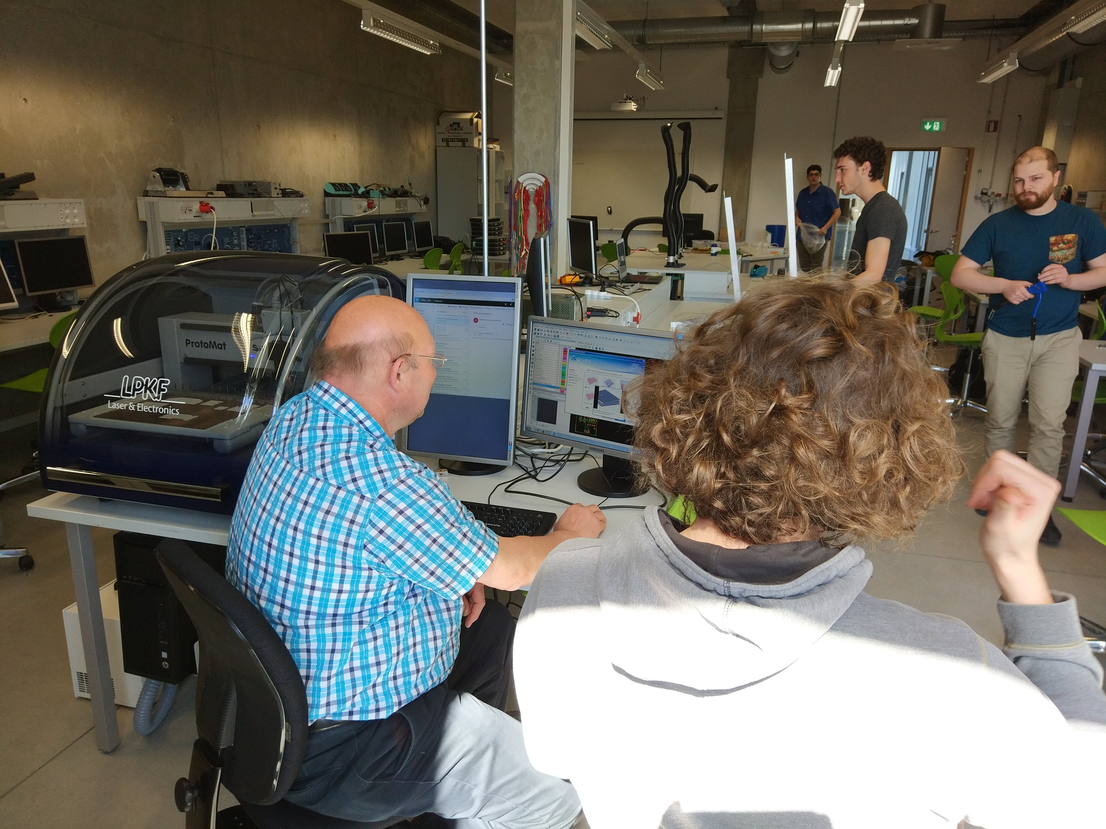
docs/photos/IMG_20170327_133126.jpg
