ccmteamap/robot/docs/photos/IMG_20170327_133128.jpg

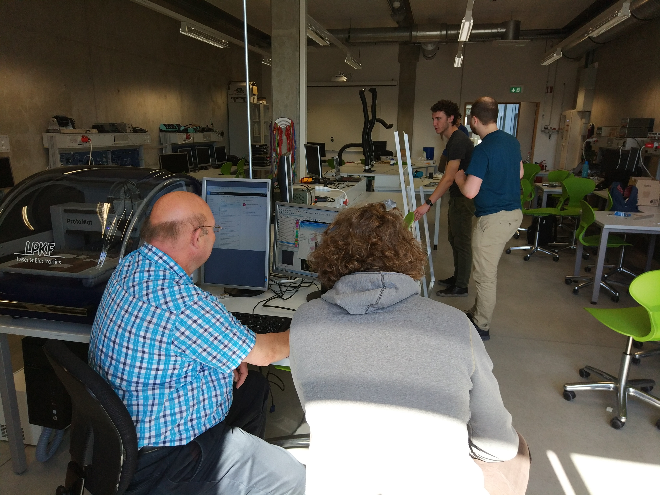
docs/photos/IMG_20170327_133128.jpg
