ccmteamap/robot/docs/photos/IMG_20170327_135606.jpg

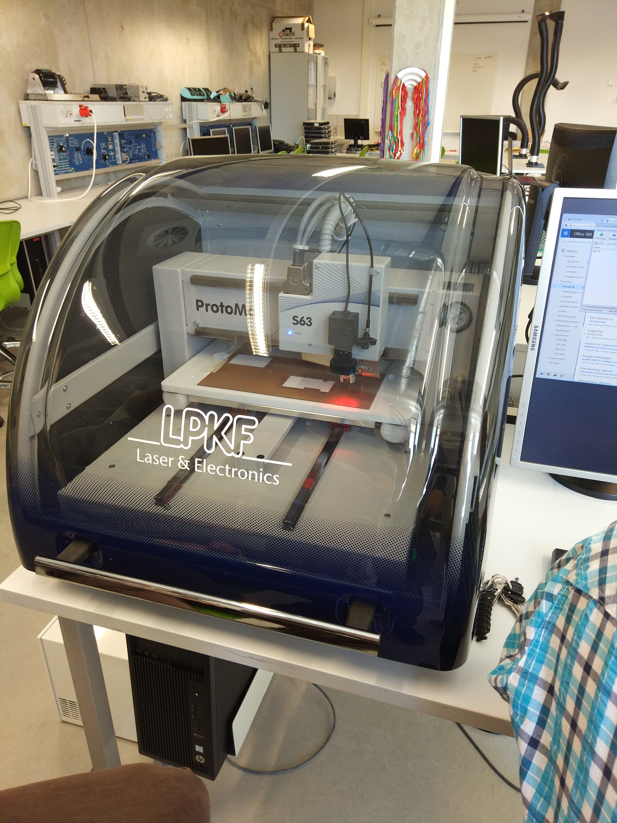
docs/photos/IMG_20170327_135606.jpg
