ccmteamap/robot/docs/photos/IMG_20170327_135611.jpg

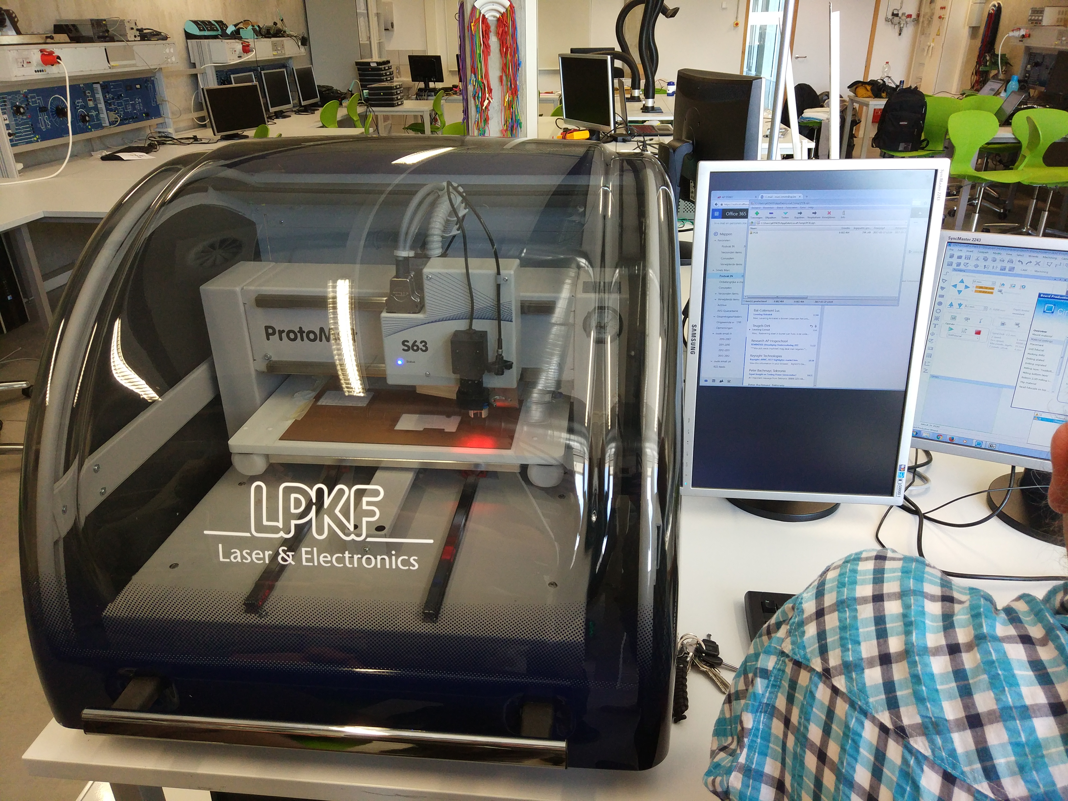
docs/photos/IMG_20170327_135611.jpg
