ccmteamap/robot/docs/photos/IMG_20170327_135617.jpg

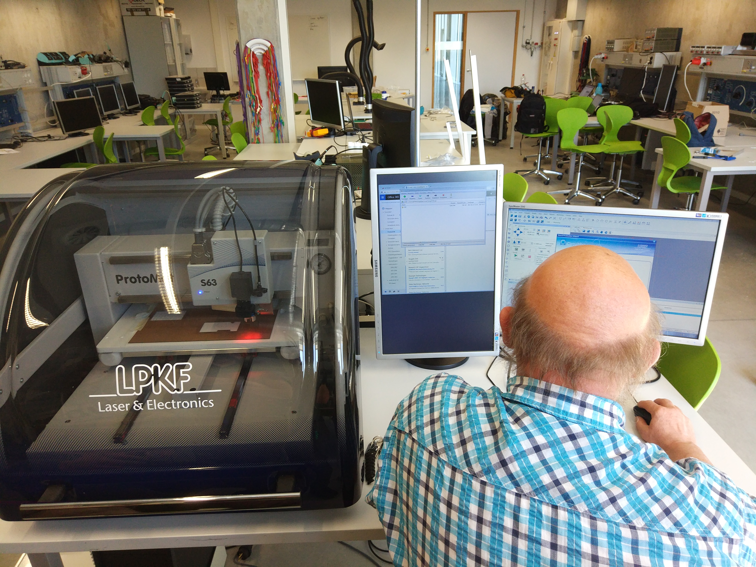
docs/photos/IMG_20170327_135617.jpg
