ccmteamap/robot/docs/photos/IMG_20170327_135621.jpg

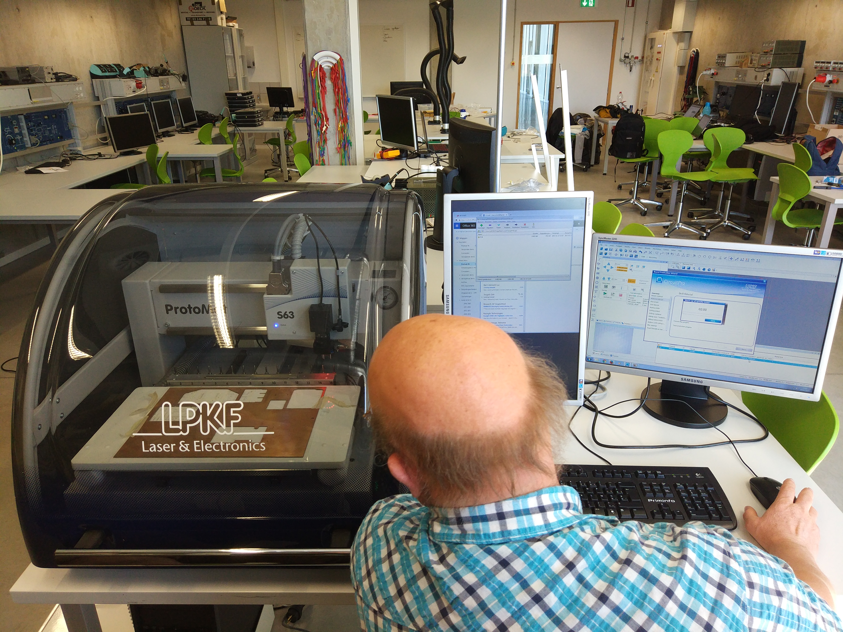
docs/photos/IMG_20170327_135621.jpg
