ccmteamap/robot/docs/photos/IMG_20170327_135622.jpg

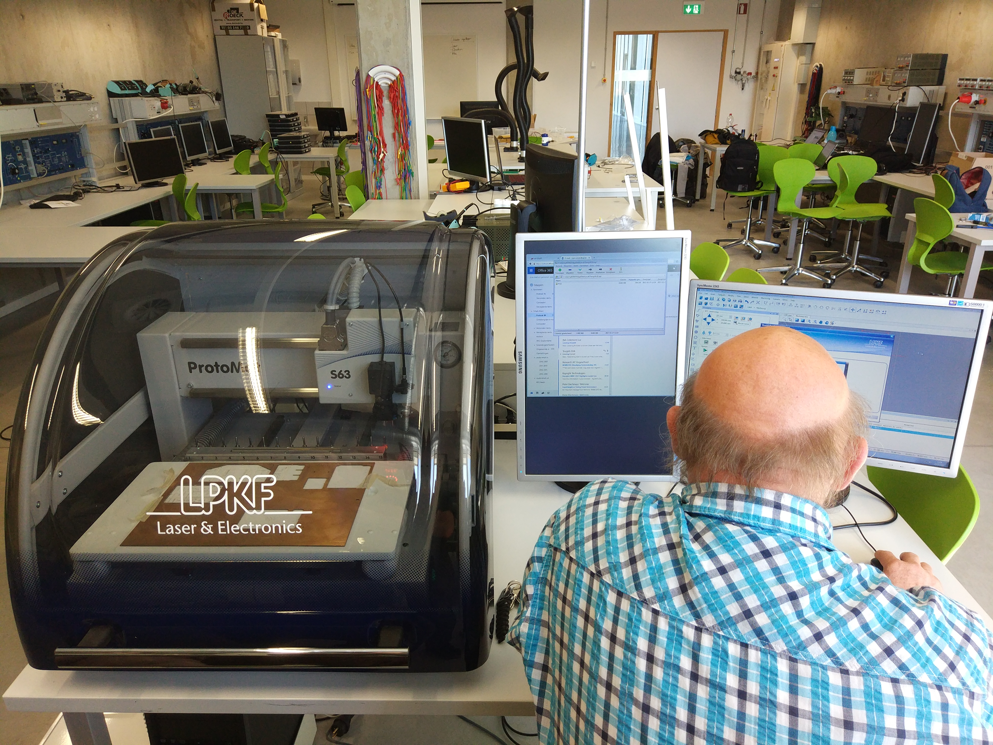
docs/photos/IMG_20170327_135622.jpg
