ccmteamap/robot/docs/photos/IMG_20170327_135720.jpg

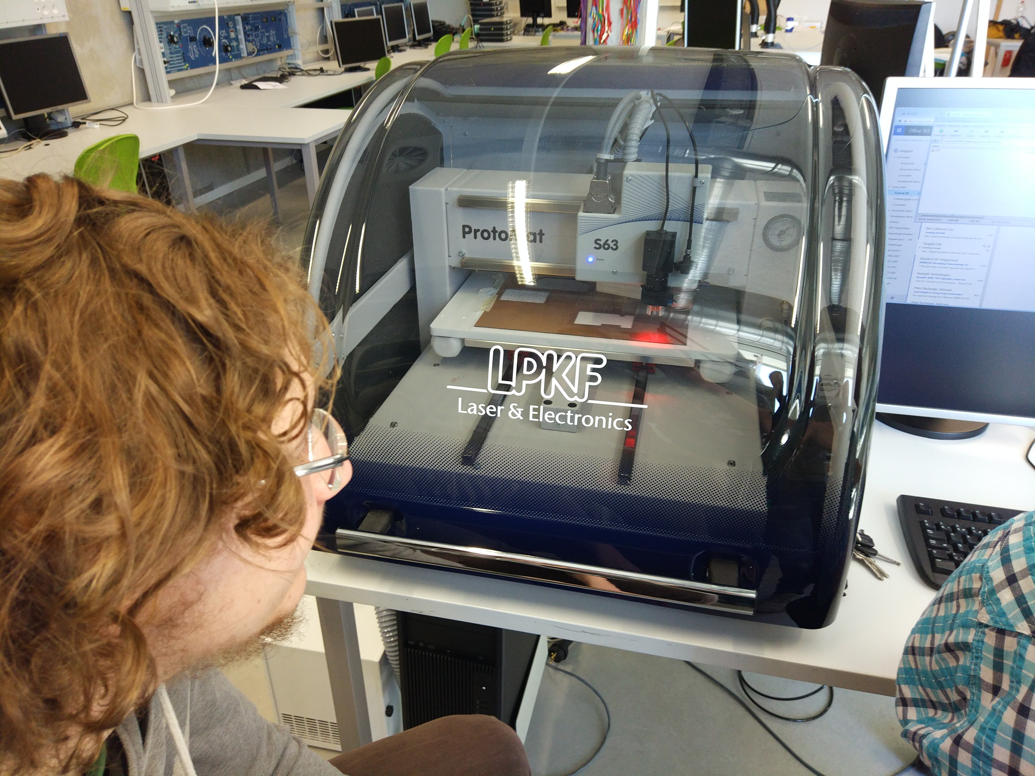
docs/photos/IMG_20170327_135720.jpg
