ccmteamap/robot/docs/photos/IMG_20170327_135722.jpg

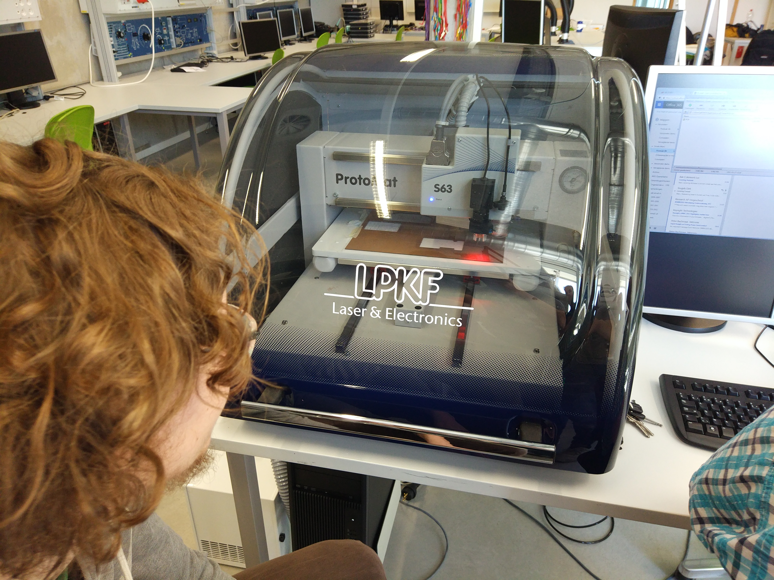
docs/photos/IMG_20170327_135722.jpg
