ccmteamap/robot/docs/photos/pb.png

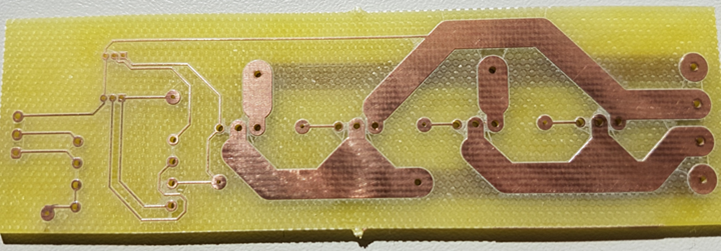
docs/photos/pb.png
