ccmteamap/robot/docs/presentatiefotos/aandrijving.PNG

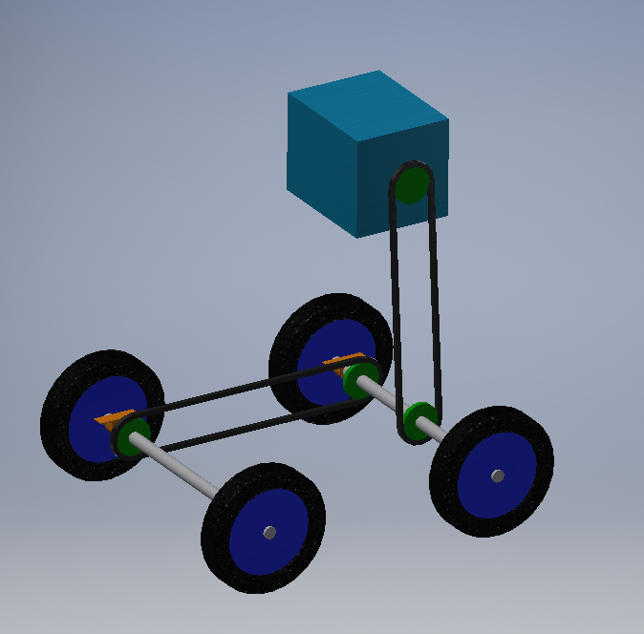
docs/presentatiefotos/aandrijving.PNG
