ccmteamap/robot/docs/presentatiefotos/EmmerAnimatie.gif

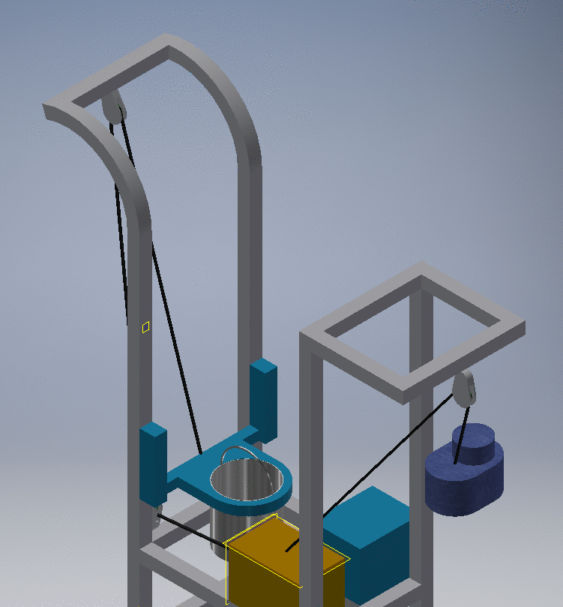
docs/presentatiefotos/EmmerAnimatie.gif
