ccmteamap/robot/docs/presentatiefotos/overzicht.PNG

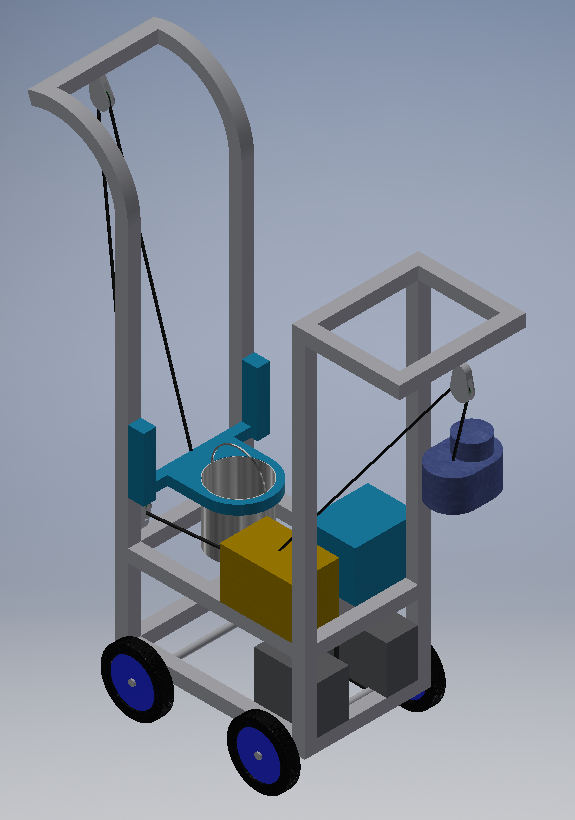
docs/presentatiefotos/overzicht.PNG
