ccmteamap/robot/docs/presentatiefotos/semi technishe tekening.PNG

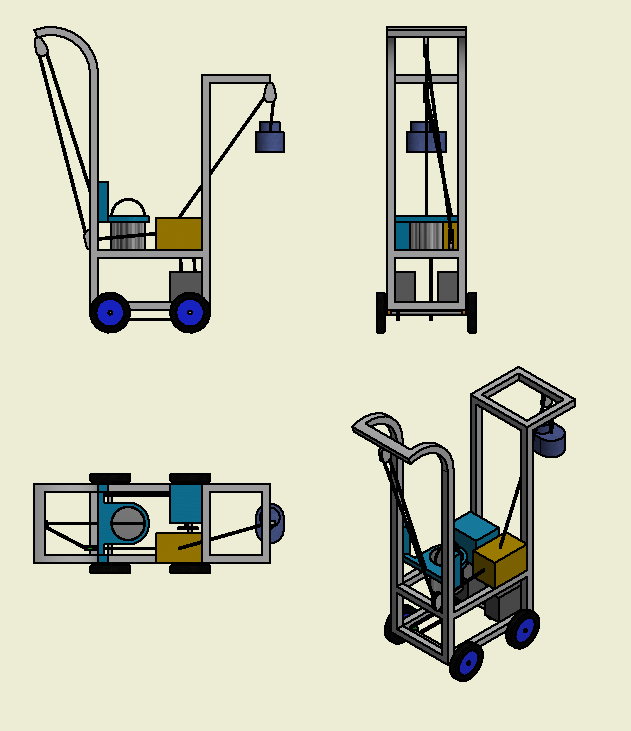
docs/presentatiefotos/semi technishe tekening.PNG
