ccmteamap/robot/docs/Schema's/Graphset/DSC_0061.JPG

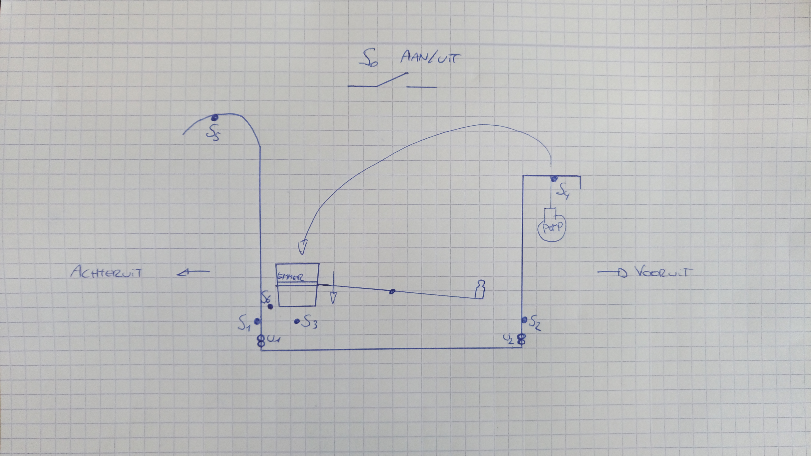
docs/Schema's/Graphset/DSC_0061.JPG
