ccmteamap/robot/DRIVING/src/client/debug.h

#ifndef DEBUG_H
#define DEBUG

#include<stdint.h>
#include"states.h"

#define DEBUG_MOTOR 0x01
#define DEBUG_DISTANCE 0x02
#define DEBUG_STATE 0x04
#define DEBUG_SENSORS 0x08
#define DEBUG_START 0x10
#define DEBUG_STOP 0x20

typedef struct {
  uint8_t id;
  int speed;
  unsigned int power;
} Motor_Info;

typedef struct {
  double emmerDistance;
  double pompDistance;
} Distance_Info;

typedef struct {
  State state;
} State_Info;

typedef struct {
  int sensorMask;
} Sensors_Info;

typedef union {
  Motor_Info motorInfo;
  Distance_Info distanceInfo;
  State_Info stateInfo;
  Sensors_Info sensorsInfo;
} Debug_Body;

typedef struct {
  uint8_t type;
  Debug_Body body;
} Debug_Message;

#endif
