ccmteamap/robot/docs/Schema's/Graphset/DSC_0060.JPG

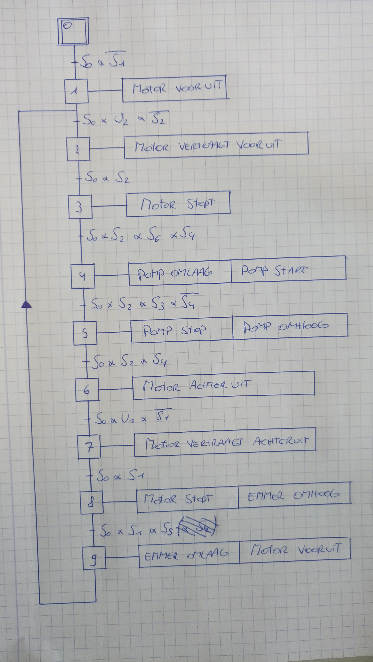
docs/Schema's/Graphset/DSC_0060.JPG
